rahulk29/stac-pcb/Files_for_BoardHouse/Files_for_Sierra/Final/231212_sierra_stackup_stac.pdf

# STACKUP & IMPEDANCE REPORT

Page 1 of 1

### Planner: ROOPAT Confidential / Proprietary Information Customer Required Finished Thickness: 55.00 (+5.50 / -5.50) mils

### Measured: Over mask on plated copper

### Job Name: Customer:

ch1593117-2

### Part Name:

### University of California, Berkeley STAC-V1

Revision: | Estimated Finish Thickness: 55.39 mils

### Data not provided

### Preliminary stack up:Reference only

### Stackup Notes:

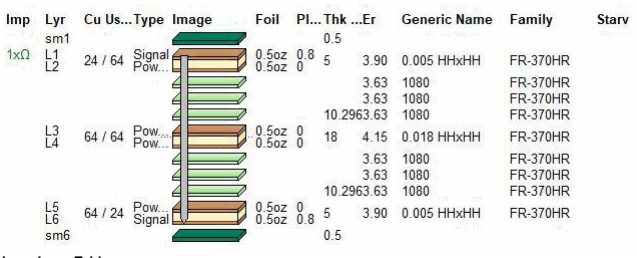
[picture p11: figure]

Index | Layer | Required Impedance [ohms] | Tol [ohms] +/- | Type | Ref 1 | Ref 2 | Orig LW [mil] | Orig Spacing [mil] | Orig CP Spacing [mil] | Finished LW [mil] | Finished Spacing [mil] | Fin. CP Spacing [mil] | Impedance Simulation [ohms] | Impedance before Mask [ohms] | IMG
a | 1 | 50 | 10% | SE Coated | | 2 | 8.10 | | | 8.50 | | | 49.7

Impedance Table

Report Version 1.60 | Report Print Date/Time: 11/21/2023 2:43:06PM | Page 1 of 1
