rahulk29/stac-pcb/schematic_review_v1/231027_bom.pdf

Purchase List: ASMPCB-STAC-V1 | Printed : 10/26/2023 2:18:02 PM

# ASMPCB-STAC-V1

ASMPCB-STAC-V1

Quantity to Build: | 1
Part List Revision: List Release Date: | A
| 10/26/2023
C:\Users\aflynn\data\PS_stuff\BWRC.mdb | Purchase List Number: | 001
Item | Qty | Part Number | Description | Reference
Vendor Name | Vendor Part Number | Manf Name | Manf Part Number
Loc | Sort Code
1 | 1 | BW-023-157 | IC custom STAC-V1 die 64 pins 0.5mm pitch QFN-64 w/EP BWRC

U6

| | DIE-CUSTOM STAC-V1
| | None

*B3

2 | 2 | BW-367-353 | Cap ceramic 0.47uF 10V 10% X7R 0603 Yageo CC0603KRX7R6BB474

C9 C12

| | CAPC-0603 0.47uF 10V
| | Digi-Key 311-1798-1-ND | Yageo CC0603KRX7R6BB474

*A2

3 | 4 | BW-171-235 | Cap ceramic 4.7uF 35V 10% X5R 0603 Murata GRM188R6YA75KE15D

C7 C8 C10 C11

| | CAPC-0603 4.7uF 35V
| | Digi-Key 490-7205-1-ND | Murata GRM188R6YA75KE15D

*A3

4 | 3 | BW-510-530 | Con 16 pin 100 mil pitch 2x8 TSW str male thru Samtec TSW-108-07-L-D

J12 J14 J15

| | CON-100 TSW 16
| | Digi-Key SAM1030-08-ND | Samtec TSW-108-07-L-D

*A8

5 | 1 | BW-350-204 | Con 6 pin 2.5mm pitch 2x3 Nano Fit RA male thru shrouded Molex 1053141106

J5

| | CON-2.5MM Nano Fit 6
| | Digi-Key WM16908-ND | Molex 1053141106

*B1

6 | 7 | BW-867-891 | Con SMA female jack end launch 50 ohm 18GHz PCB long pin (f/62mil board) Cinch 142-0701-801 J6 J8 J10 J11 J13 J16 J17
| | CON-RF SMA edge mnt
| | Digi-Key J502-ND | Cinch 142-0701-801

*B2

7 | 2 | BW-746-991 | IC LT3042 adj LDO regulator 200mA MSOP-EP-10 Analog Devices LT3042IMSE#TRPBF

U4 U5

| | IC LT3042
Digi-Key LT3042IMSE#TRPBFCT-ND | Analog Devices LT3042IMSE#TRPBF

*B4

ASMPCB-STAC-V1

Item | Qty | Part Number | Description | Reference
Vendor Name | Vendor Part Number | Manf Name | Manf Part Number
Loc | Sort Code
8 | 1 | BW-849-997 | IC LT3083 LDO regulator 3A DDPAK-5 Analog Devices LT3083EQ#PBF

U2

| | IC LT3083
Digi-Key 505-LT3083EQ#PBF-ND | Analog Devices LT3083EQ#PBF

*B5

9 | 1 | BW-747-432 | LED 565nm (green) 2.2V 0603 surface-mount Lumex SML-LX0603GW-TR

D1

| | LED green
| | Digi-Key 67-1549-1-ND | Lumex SML-LX0603GW-TR

*B7

10 | 1 | BW-471-924 | MOSFET N-CH dual 60V 35A SOT-1205 Nexperia BUK9K12-60EX

U1

| | Q-NMOS BUK9K12-60EX
| | Digi-Key 1727-1897-1-ND | Nexperia BUK9K12-60EX

*B8

11 | 3 | BW-354-763 | Res 301 1% 1/10W 0603 Panasonic ERA-3AEB3010V

R9 R12 R13

| | R1%-0603 301
| | Digi-Key P301DBCT-ND | Panasonic ERA-3AEB3010V

*C1

12 | 1 | BW-812-714 | Res 909 1% 1/10W 0603 Panasonic ERJ-3EKF9090V

R4

| | R1%-0603 909
| | Digi-Key P909HCT-ND | Panasonic ERJ-3EKF9090V

*C2

13 | 1 | BW-446-612 | Res 15K 1% 1/10W 0603 Panasonic

R8

| | R1%-0603 15K
| | Digi-Key P15.0KHCT-ND | Panasonic ERJ-3EKF1502V

*C3

14 | 1 | BW-628-791 | Res 33.2K 1% 1/10W 0603 Panasonic ERJ-3EKF3322V

R11

| | R1%-0603 33.2K
| | Digi-Key P33.2KHCT-ND | Panasonic ERJ-3EKF3322V

*C4

ASMPCB-STAC-V1

Vendor Name | Vendor Part Number | Manf Name | Manf Part Number
Loc | Sort Code
15 | 1 | BW-131-959 | Res 82.5K 1% 1/10W 0603 Panasonic ERJ-3EKF8252V

R6

| | R1%-0603 82.5K
| | Digi-Key P82.5KHCT-ND | Panasonic ERJ-3EKF8252V

*C5

16 | 1 | BW-606-753 | Res 93.1K 1% 1/10W 0603 Panasonic ERJ-3EKF9312V

R5

| | R1%-0603 93.1K
| | Digi-Key P93.1KHCT-ND | Panasonic ERJ-3EKF9312V

*C6

17 | 1 | BW-760-287 | Res 200K 1% 1/10W 0603 Panasonic ERJ-3EKF2003V

R1

| | R1%-0603 200K
| | Digi-Key P200KHCT-ND | Panasonic ERJ-3EKF2003V

*C7

18 | 1 | BW-560-201 | Res 215K 1% 1/10W 0603 Panasonic ERJ-3EKF2153V

R7

| | R1%-0603 215K
| | Digi-Key P215KHCT-ND | Panasonic ERJ-3EKF2153V

*C8

19 | 1 | BW-514-032 | Res 510K 1% 1/10W 0603 Panasonic ERJ-3EKF5103V

R2

| | R1%-0603 510K
| | Digi-Key P510KHCT-ND | Panasonic ERJ-3EKF5103V

*D1

20 | 1 | BW-421-162 | Res 2.7M 5% 1/10W 0603 Panasonic ERJ-3GEYJ275V

R3

| | R5%-0603 2.7M
| | Digi-Key P2.7MGCT-ND | Panasonic ERJ-3GEYJ275V

*D2

21 | 1 | BW-257-784 | Res var trimmer pot 5K 1/4W 3-pin SMT Bourns 3214X-1-502E

R10

| | RVAR 5K
Digi-Key 3214X-1-502ECT-ND | Bourns 3214X-1-502E

*D3

ASMPCB-STAC-V1

Vendor Name | Vendor Part Number | Manf Name | Manf Part Number
Loc | Sort Code
22 | 1 | BW-431-238 | Switch slide SPDT ST thru Wurth 450301014042

S1

| | SW SPDT
Digi-Key 450301014042-ND | Wurth 450301014042

*D4

23 | 1 | BW-966-768 | Test point loop 63mil dia hole black Keystone 5006

T9

| | TEST-PT 1
| | Digi-Key 36-5006-ND | Keystone 5006

*D6

24 | 2 | BW-220-198 | Con 12 pin 100 mil pitch 2x5 TSW RA male thru 0.230" post height Samtec TSW-106-08-L-D-RA J7 J9
| | CON-100 TSW 12
| | Digikey SAM1041-06-ND | Samtec TSW-106-08-L-D-RA

*A7

25 | 1 | BW-663-053 | Cap ceramic 0.1uF 16V 5% X7R 0603 Kemet C0603C104J4RACTU

C6

| | CAPC-0603 0.1uF 16V
| | Mouser 80-C0603C104J4R | Kemet C0603C104J4RACTU

*A1

Digi-Key 399-1097-1-ND

26 | 10 | BW-224-068 | Cap ceramic 10uF 25V 20% X5R 0603 Murata GRM188R61E106MA73D

C4 C5 C15 C16 C17 C18 C19
C20 C21 C22
| | CAPC-0603 10uF 25V
Mouser 81-GRM188R61E106MA3D | Murata GRM188R61E106MA73D

*A4

Digi-Key 490-7202-1-ND

27 | 5 | BW-998-821 | Cap aluminum polymer 220uF 16V 20% SMD, 6.3mm dia. Panasonic 16SVPK220M

C1 C2 C3 C13 C14

| | CAPE-AL-GP 220uF 16V
| | Mouser 667-16SVPK220M | Panasonic 16SVPK220M

*A5

28 | 4 | BW-517-054 | Con 3 pin 100 mil pitch 1x3 TSW str male thru 0.230" post height Samtec TSW-103-07-G-S

J1 J2 J3 J4

| | CON-100 TSW 3
| | Mouser 200-TSW10307GS | Samtec TSW-103-07-G-S

*A6

Digi-Key SAM1029-03-ND

ASMPCB-STAC-V1

Vendor Name | Vendor Part Number | Manf Name | Manf Part Number
Loc | Sort Code
29 | 1 | BW-843-693 | IC LTC4365CTS8#TRMPBF
Analog Devices LTC4365 Surge Surpressor

U3

IC LTC4365CTS8#TRMPBF

Mouser | 584-C4365CTS8TRMPBF | Analog Devices | LTC4365CTS8#TRMPBF

*B6

30 | 1 | BW-602-053 | Test point loop 63mil dia hole orange
Keystone 5008

T4

TEST-PT 1

Mouser | 534-5008 | Keystone | 5008

*D5

Digi-Key 36-5008-ND

ASMPCB-STAC-V1
