rahulk29/stac-pcb/Files_for_AssemblyHouse/Digicom_Final/240109_stac_v1_fabrication_drawing.PDF

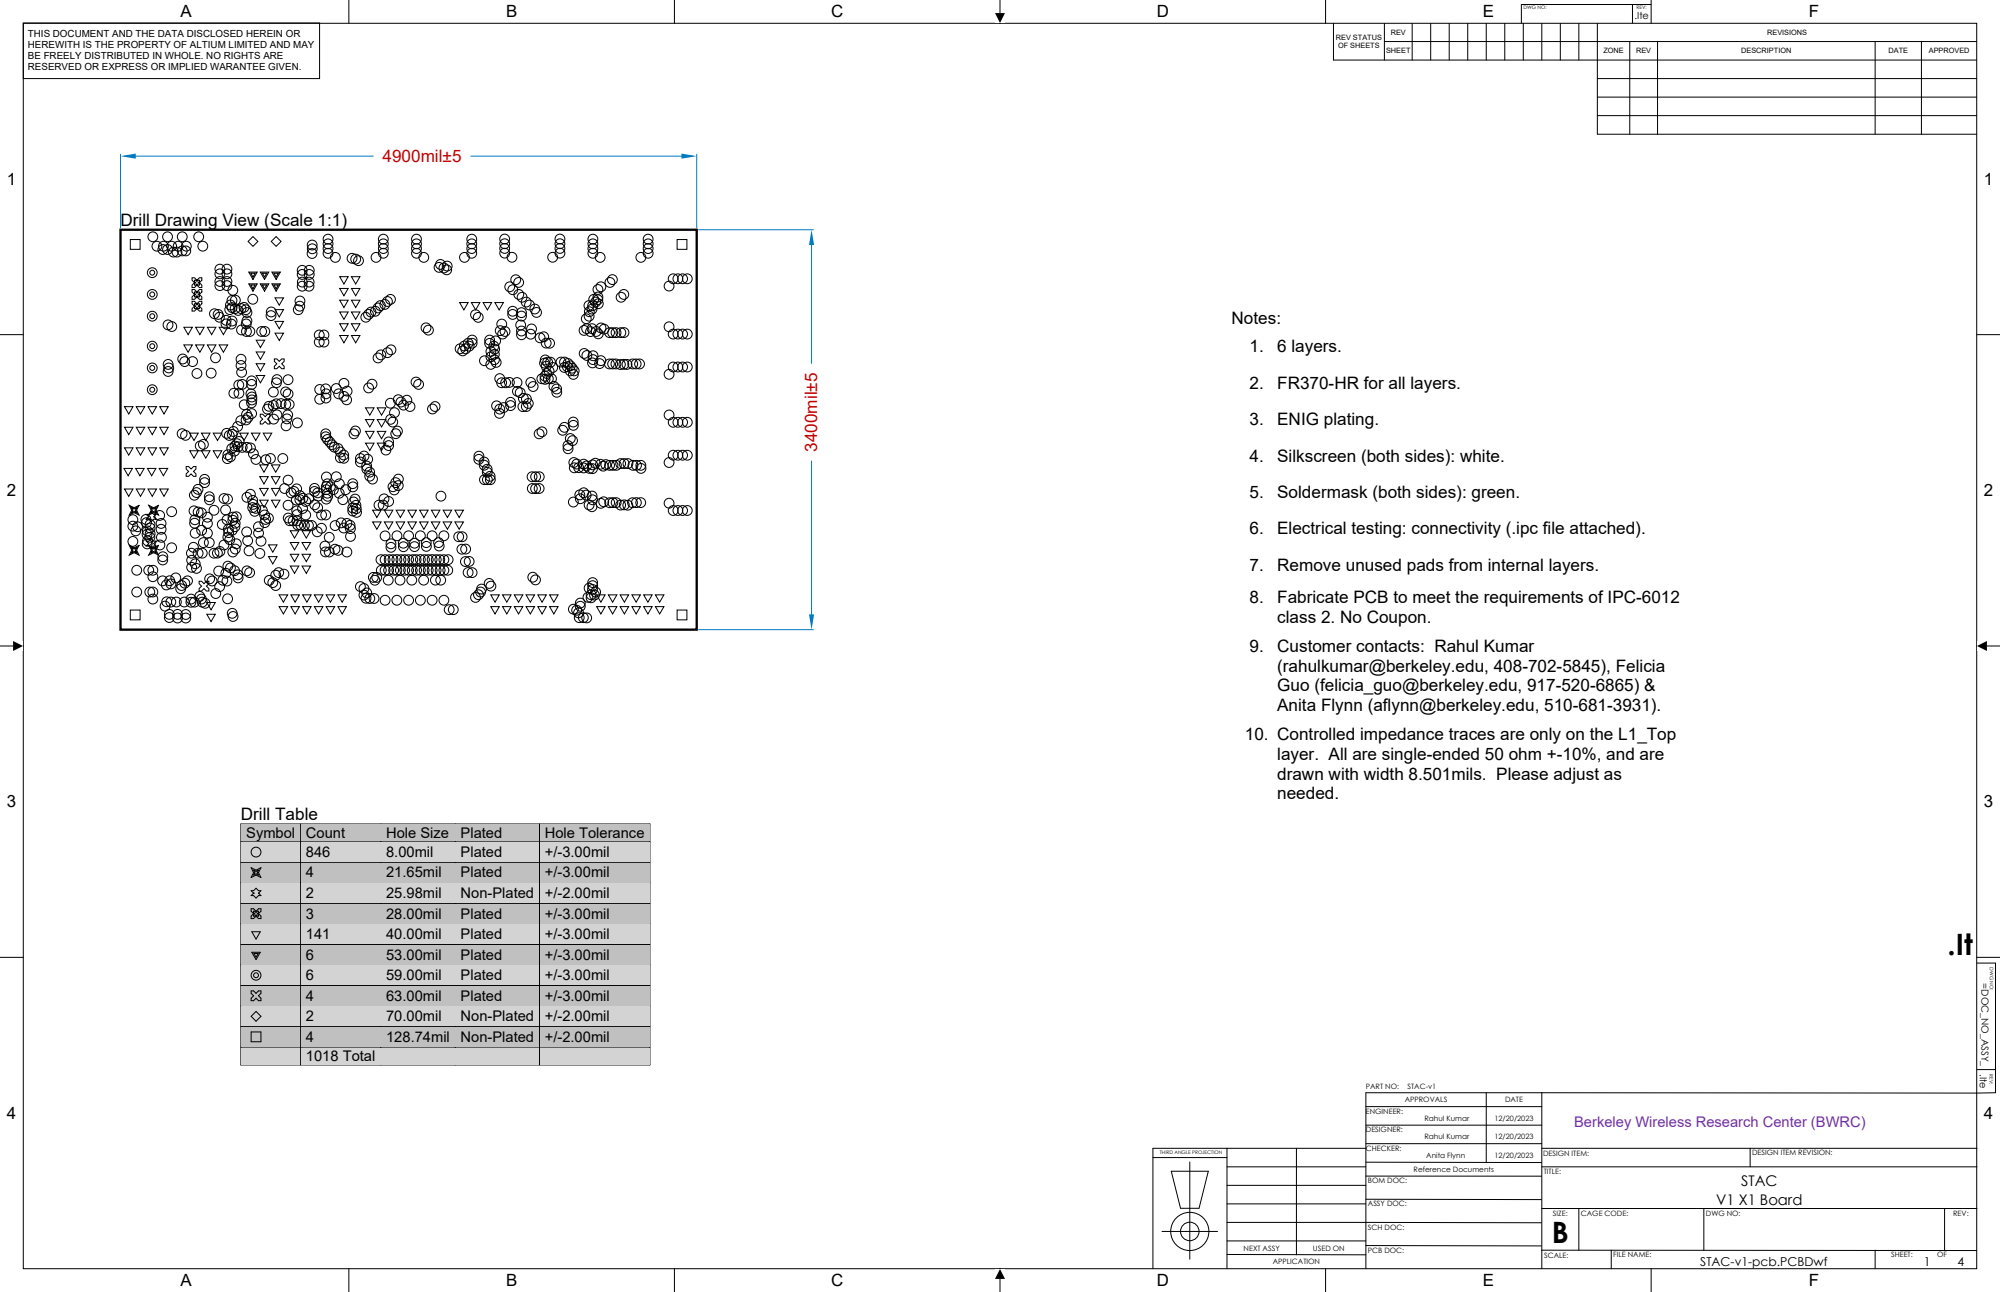
[picture p59: page 1]

HEREWITH IS THE PROPERTY OF ALTIUM LIMITED AND MAY
BE FREELY DISTRIBUTED IN WHOLE. NO RIGHTS ARE
RESERVED OR EXPRESS OR IMPLIED WARANTEE GIVEN.

Drill Drawing View (Scale 1:1)

2. FR370-HR for all layers.

4. Silkscreen (both sides): white.

5. Soldermask (both sides): green.

6. Electrical testing: connectivity (.ipc file attached).

7. Remove unused pads from internal layers.
Fabricate PCB to meet the requirements of IPC-6012
class 2. No Coupon.
Customer contacts: Rahul Kumar
(rahulkumar@berkeley.edu, 408-702-5845), Felicia
Guo (felicia_guo@berkeley.edu, 917-520-6865) &
Anita Flynn (aflynn@berkeley.edu, 510-681-3931).
Controlled impedance traces are only on the L1_Top
layer. All are single-ended 50 ohm +-10%, and are
drawn with width 8.501mils. Please adjust as
needed.

Symbol | Count | Hole Size | Plated | Hole Tolerance

846 | 8.00mil | Plated | +/-3.00mil
4 | 21.65mil | Plated | +/-3.00mil
2 | 25.98mil | Non-Plated | +/-2.00mil
3 | 28.00mil | Plated | +/-3.00mil
141 | 40.00mil | Plated | +/-3.00mil
6 | 53.00mil | Plated | +/-3.00mil
6 | 59.00mil | Plated | +/-3.00mil
4 | 63.00mil | Plated | +/-3.00mil
2 | 70.00mil | Non-Plated | +/-2.00mil
4 | 128.74mil | Non-Plated | +/-2.00mil
1018 Total

APPROVALS | DATE

ENGINEER: Rahul Kumar | 12/20/2023

Berkeley Wireless Research Center (BWRC)

DESIGNER: Rahul Kumar | 12/20/2023

THIRD ANGLE PROJECTION

CHECKER: Anita Flynn | 12/20/2023

SCH DOC:

NEXT ASSY | USED ON

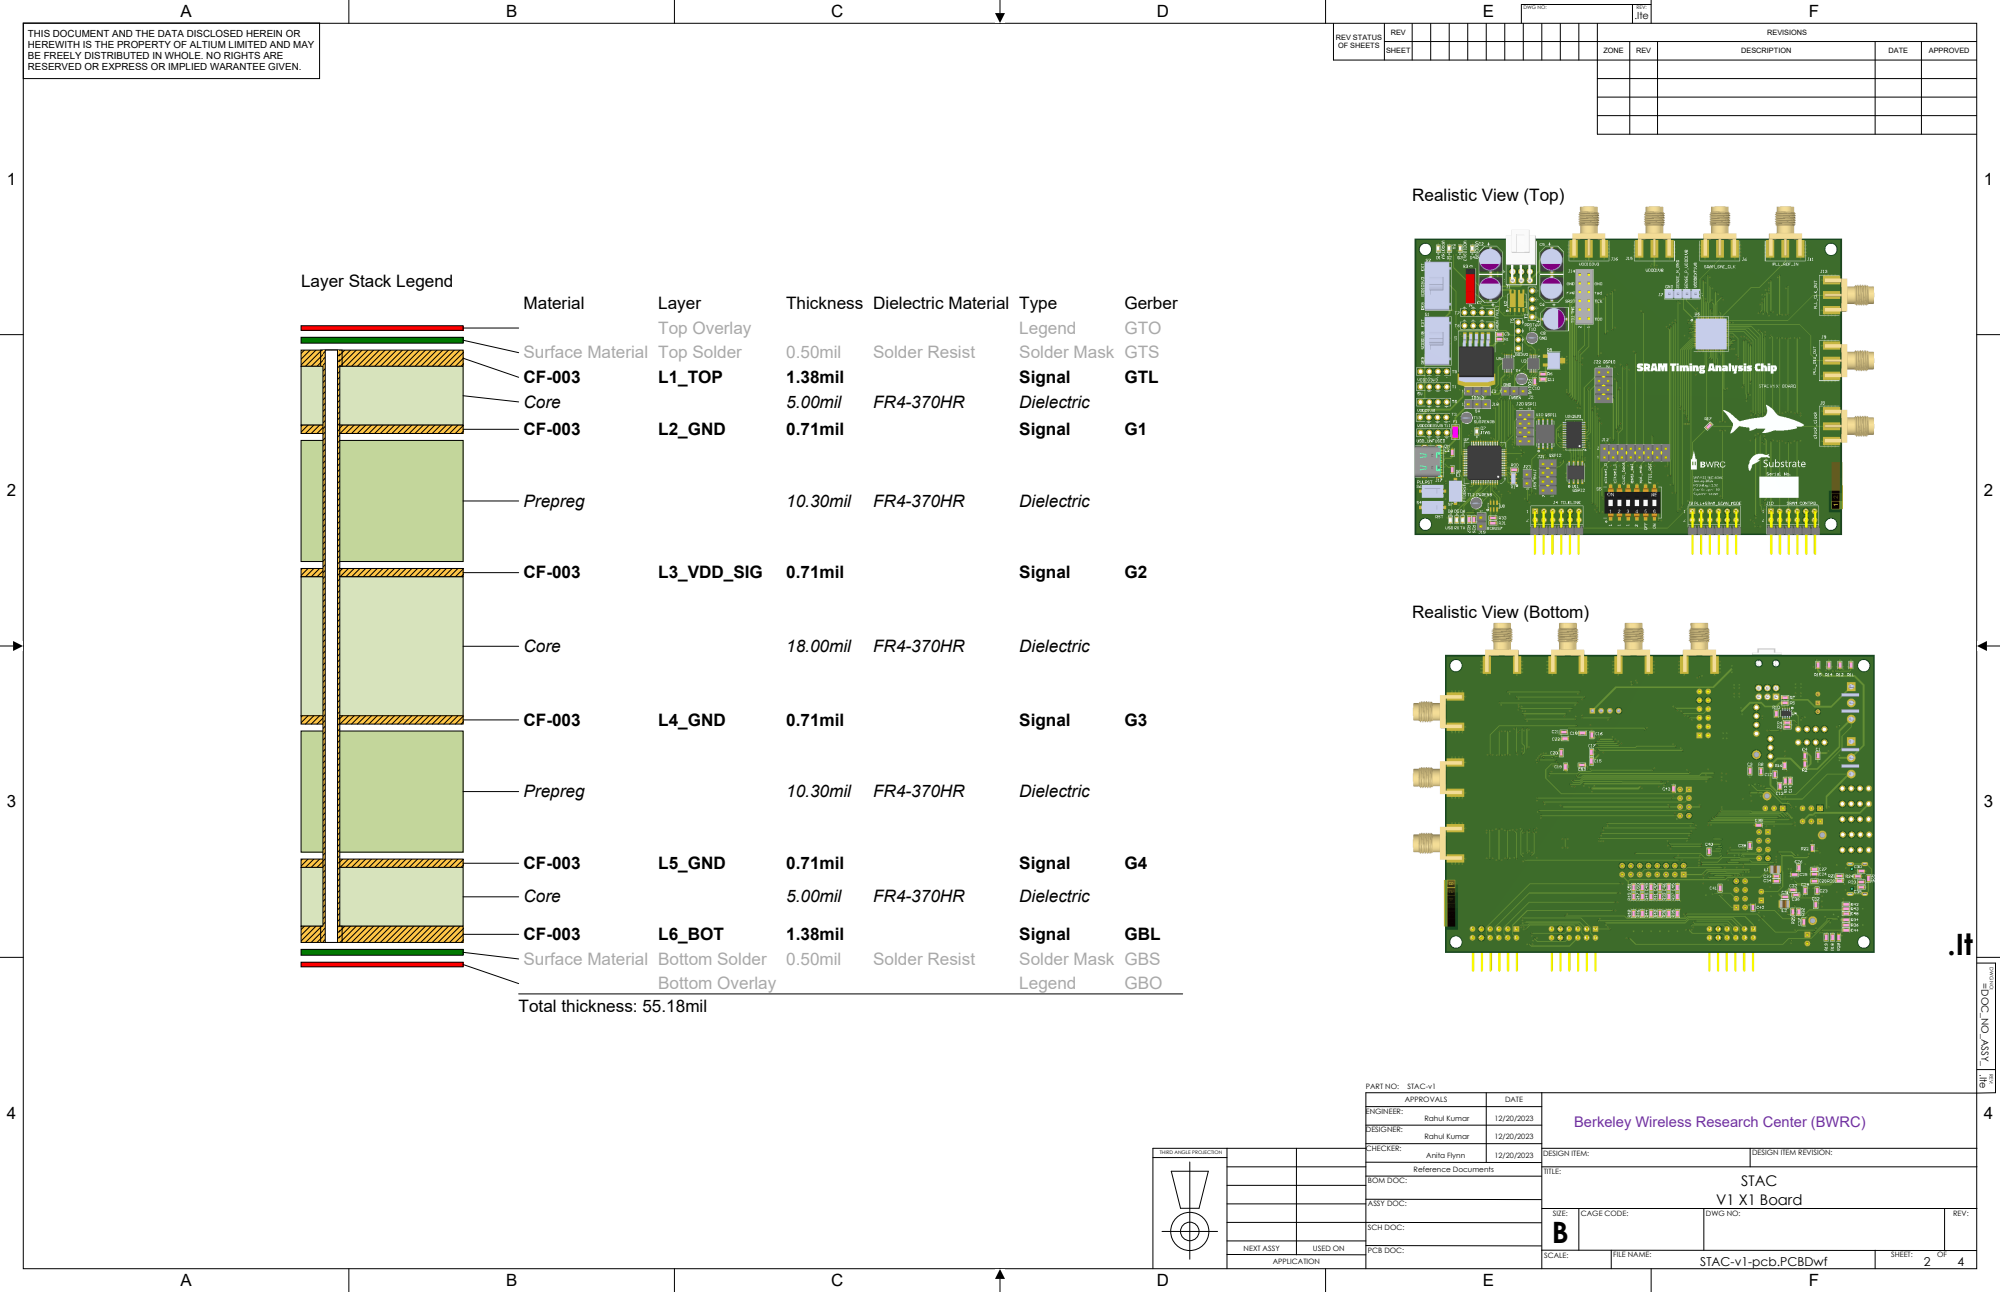
[picture p60: page 2]

APPROVALS | DATE

ENGINEER: Rahul Kumar | 12/20/2023

Berkeley Wireless Research Center (BWRC)

DESIGNER: Rahul Kumar | 12/20/2023

THIRD ANGLE PROJECTION

CHECKER: Anita Flynn | 12/20/2023

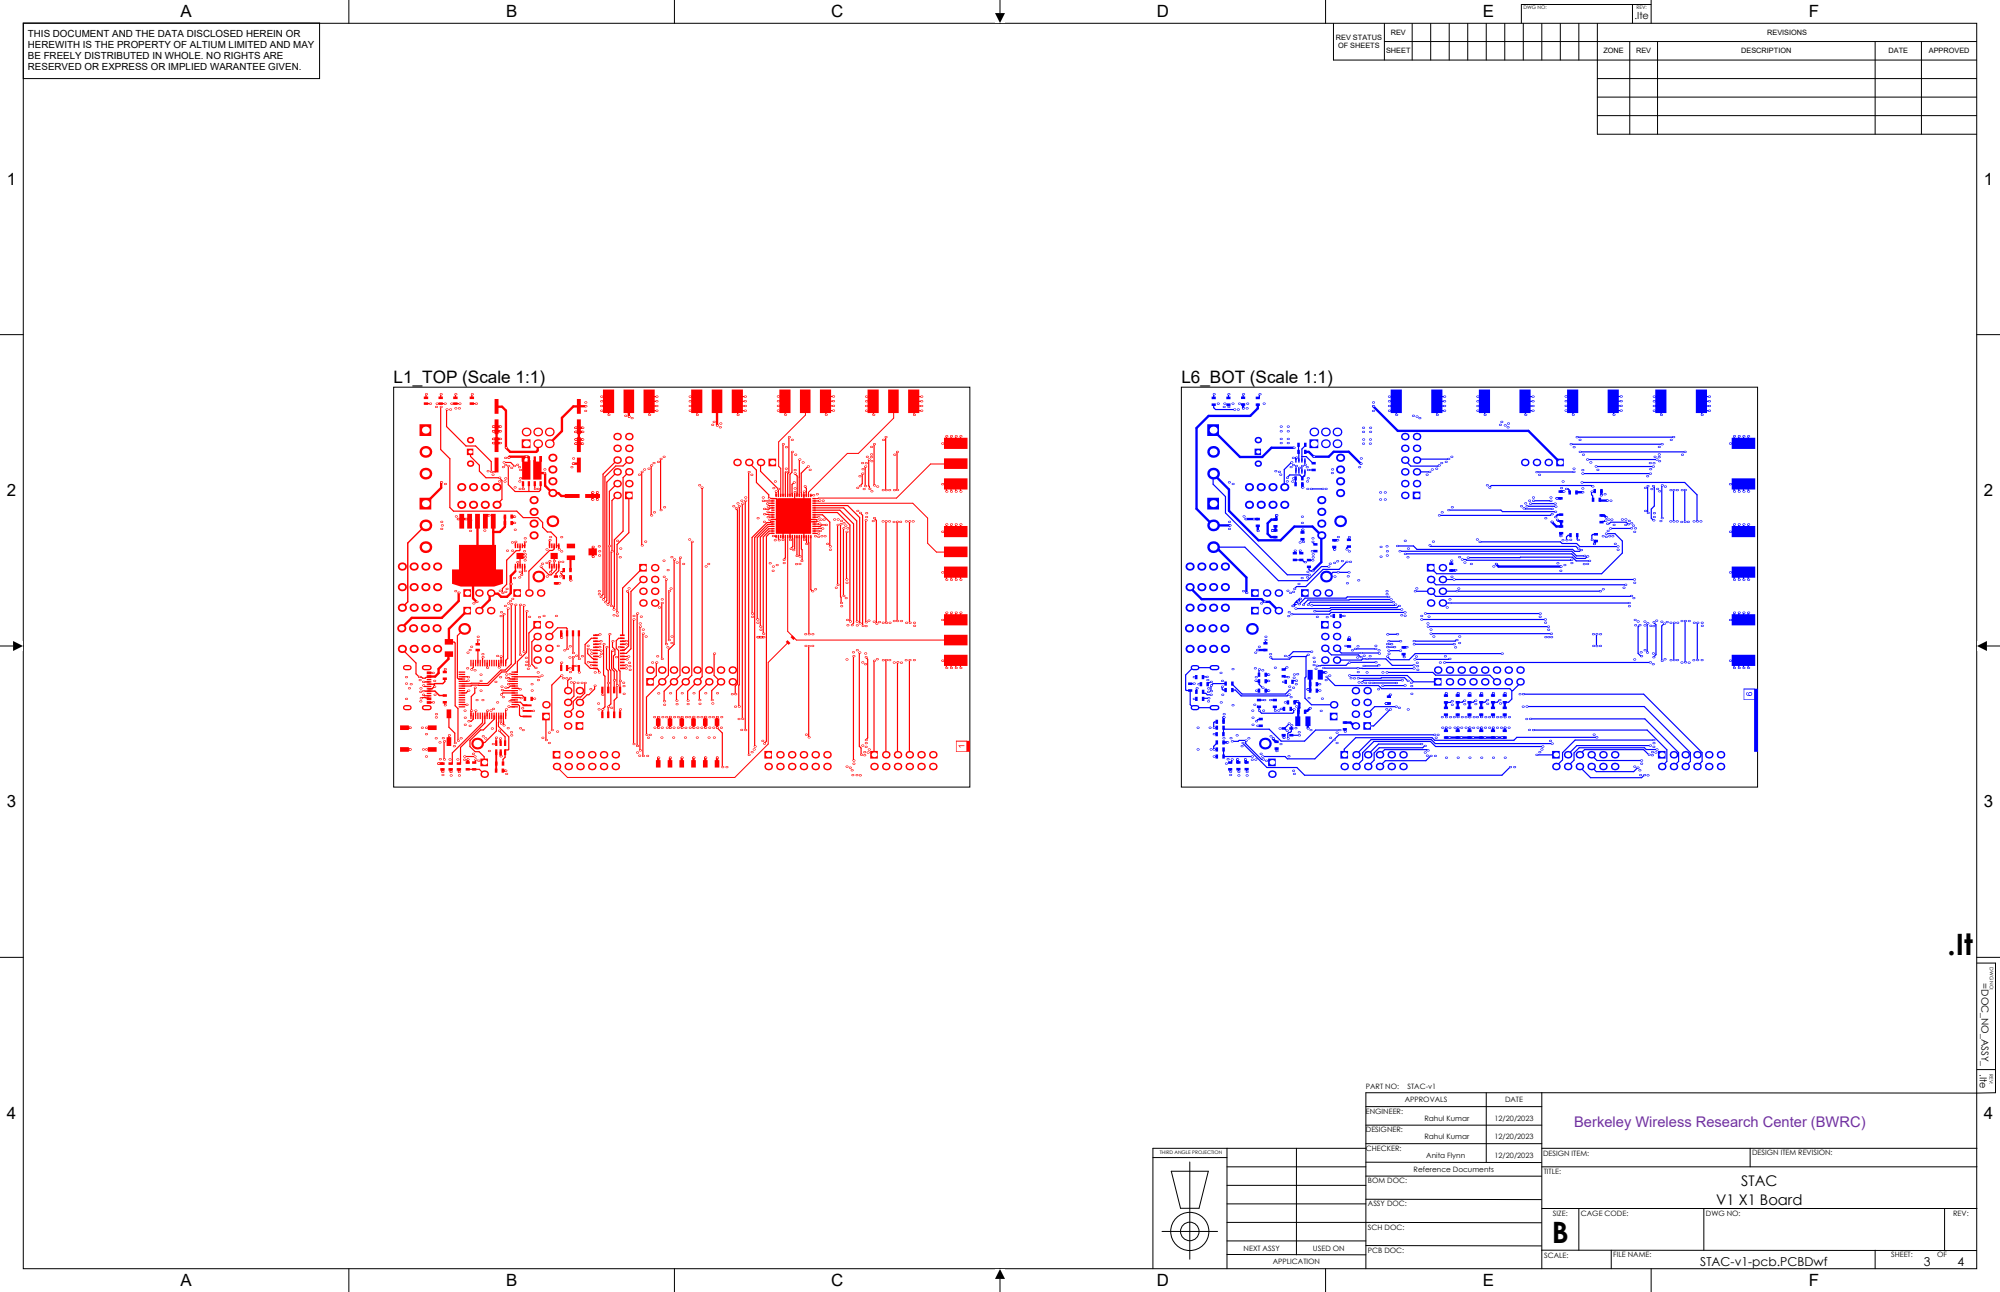
[picture p61: page 3]

Berkeley Wireless Research Center (BWRC)

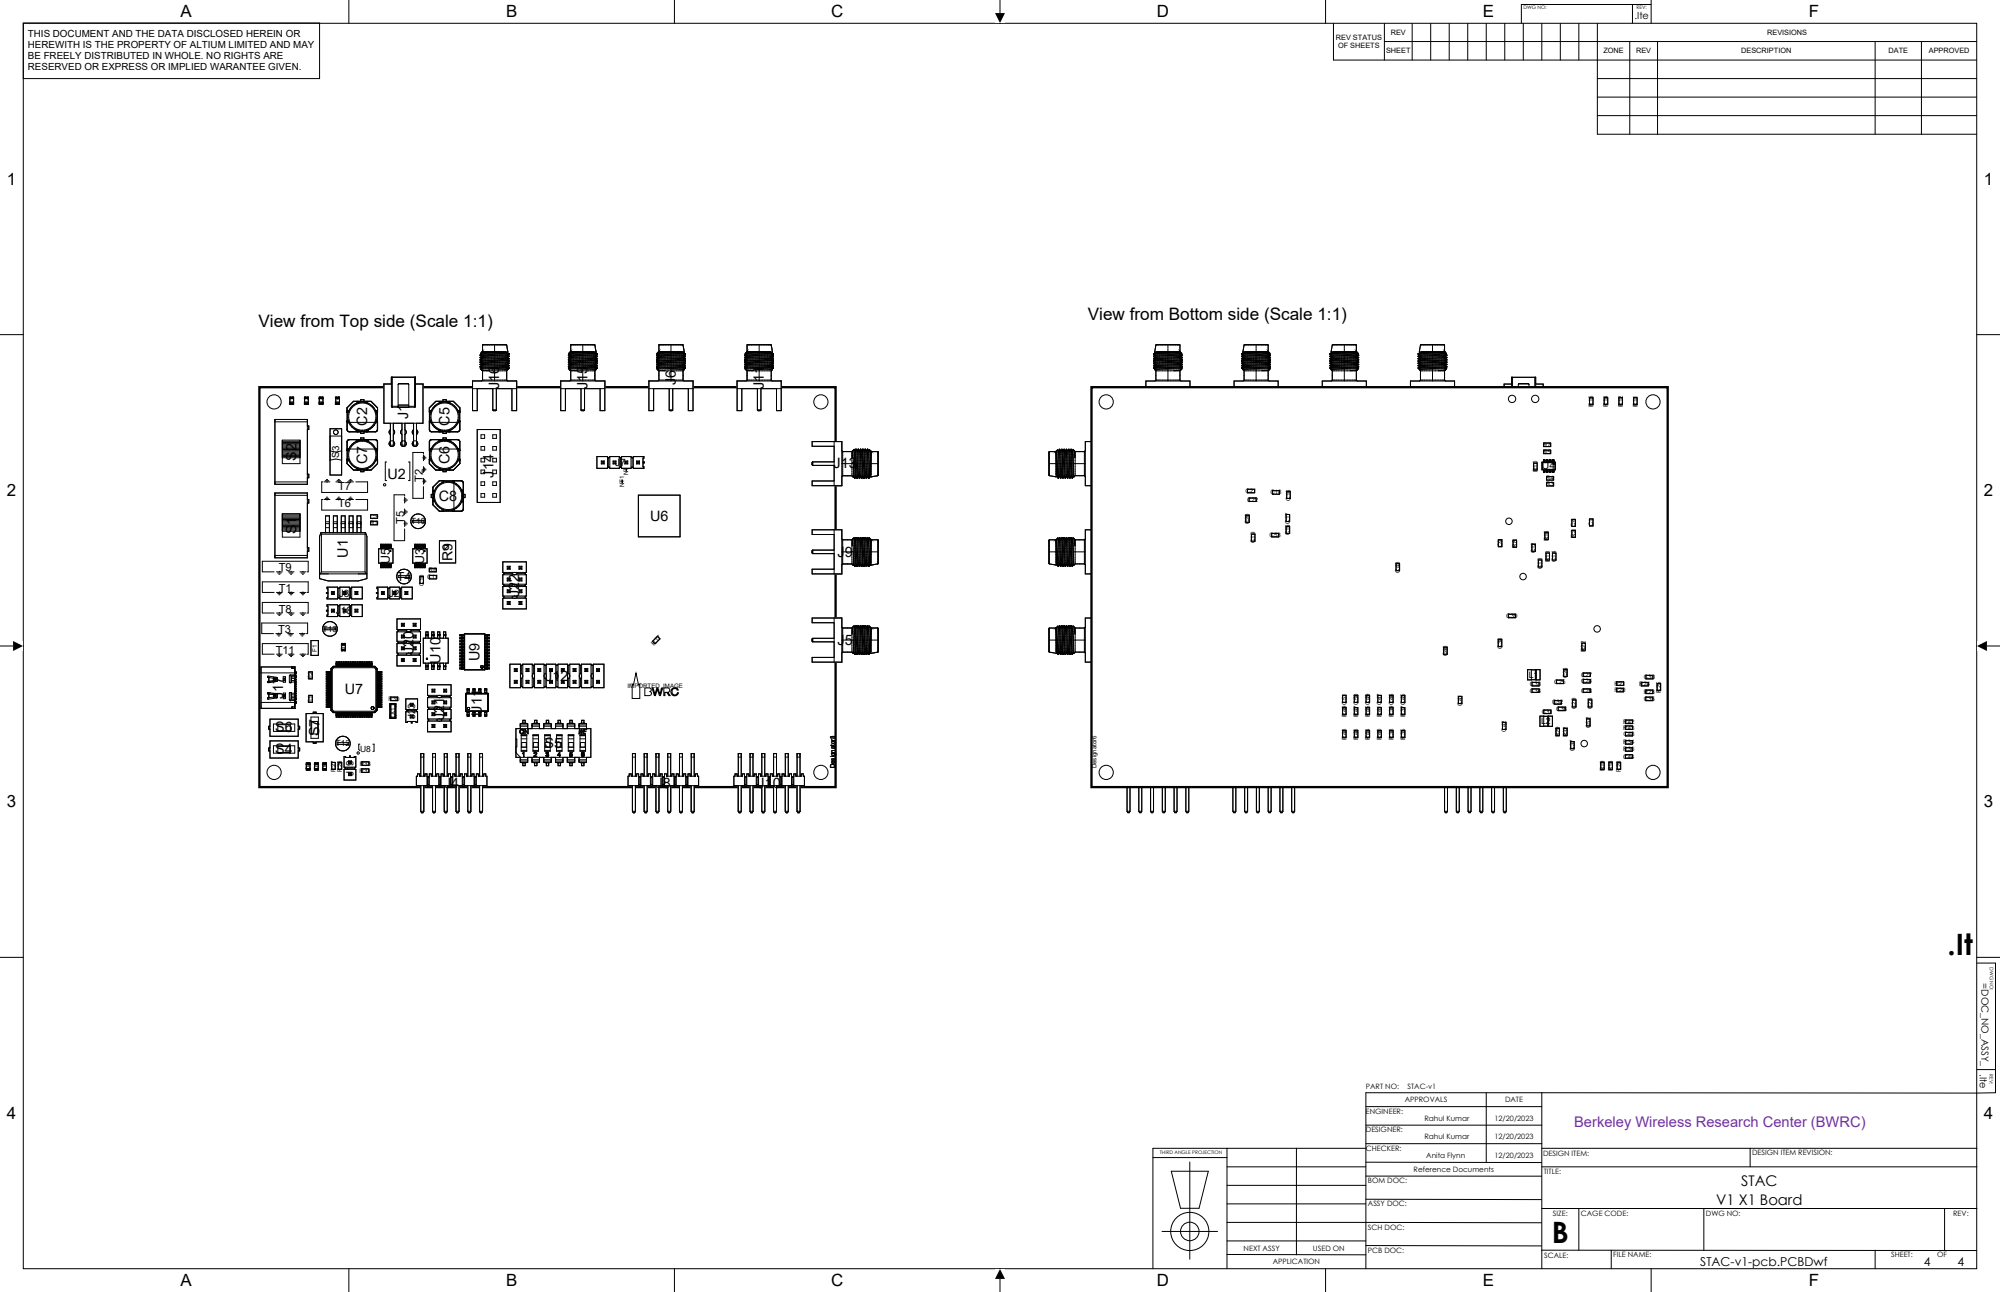
[picture p62: page 4]

View from Bottom side (Scale 1:1)

View from Top side (Scale 1:1)

Berkeley Wireless Research Center (BWRC)
