rahulk29/stac-pcb/Files_for_AssemblyHouse/Digicom_Final/240109_stac_v1_SMT.pdf

# stac-v1.bmb 1/9/2024 File By: bob@partsync.com www.PartSync.com Flags: X=no-stuff T=Thru Hole H=Hand SMT E=Error

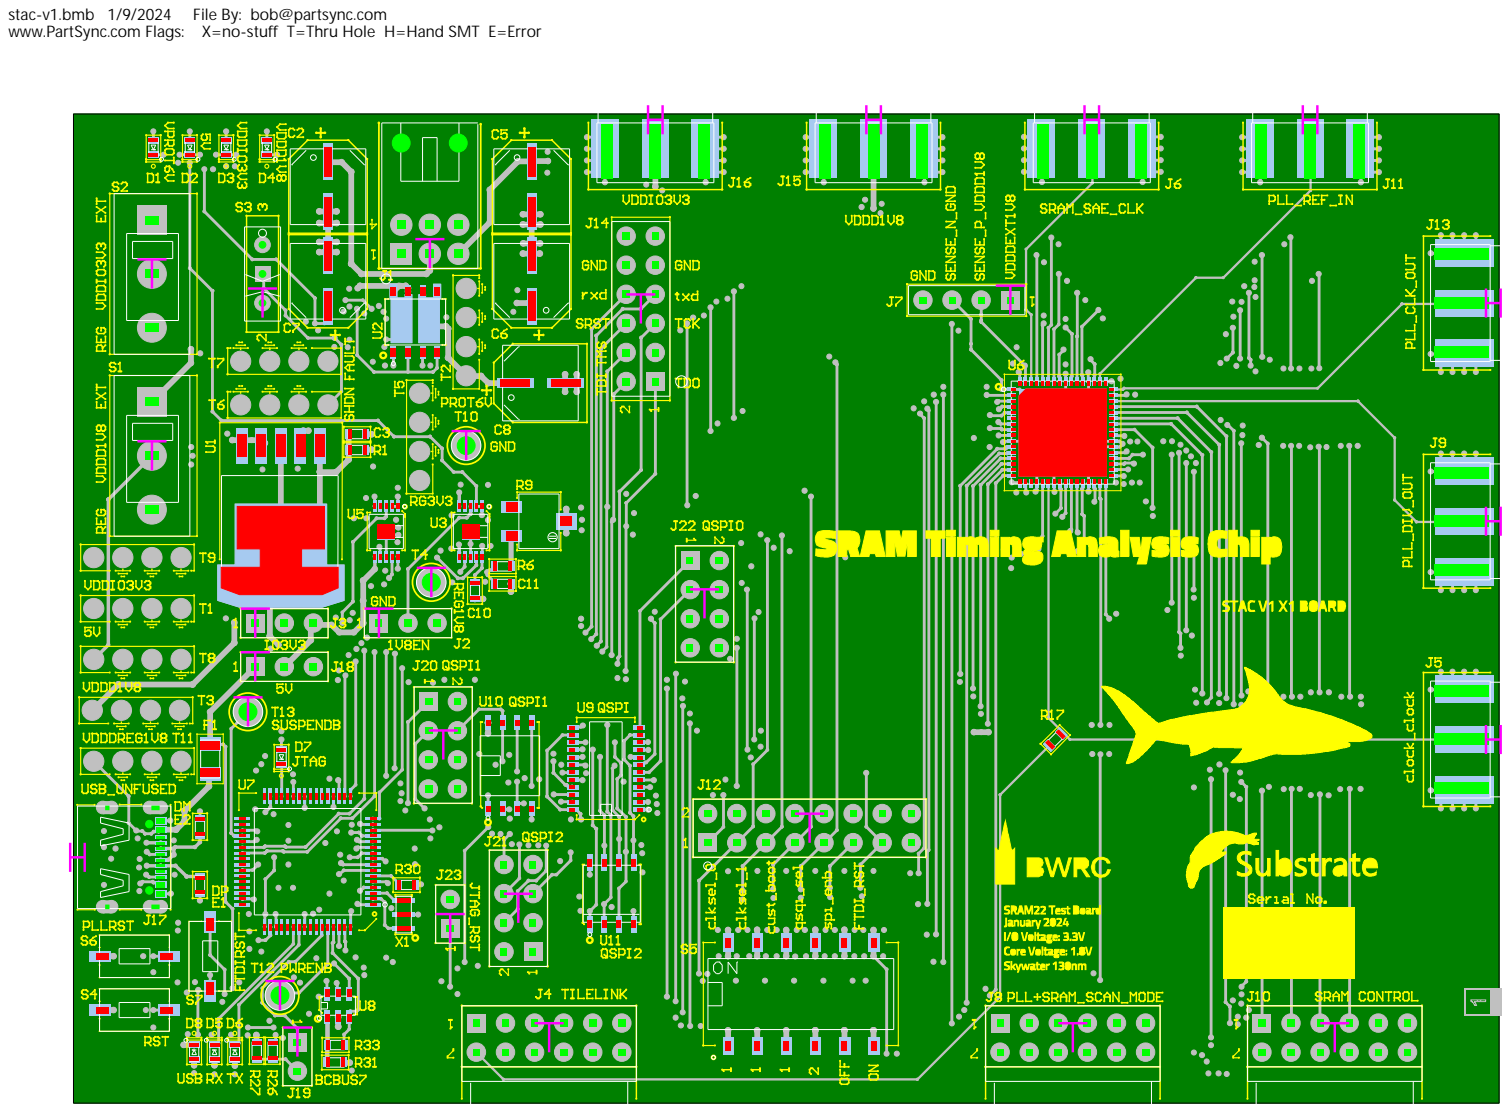
[picture p63: page 1]

# stac-v1.bmb 1/9/2024 File By: bob@partsync.com www.PartSync.com Flags: X=no-stuff T=Thru Hole H=Hand SMT E=Error

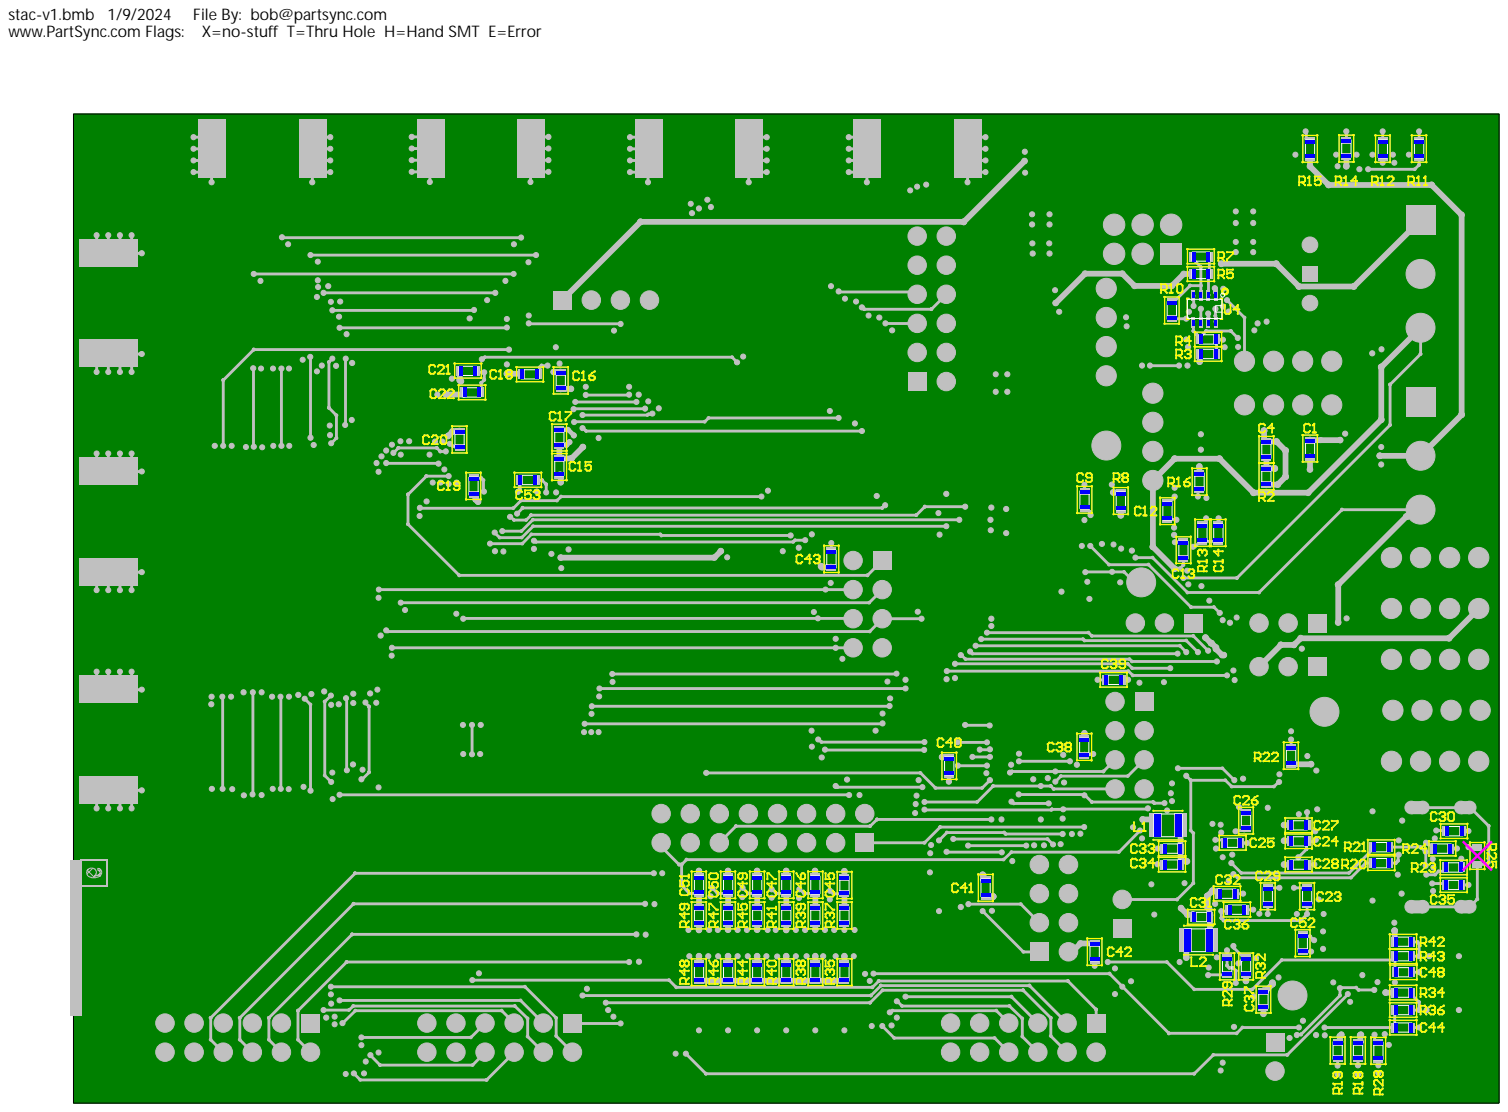
[picture p64: page 2]
