rahulk29/stac-pcb/Files_for_AssemblyHouse/Digicom_RFQ/fab_drawing_stac.pdf

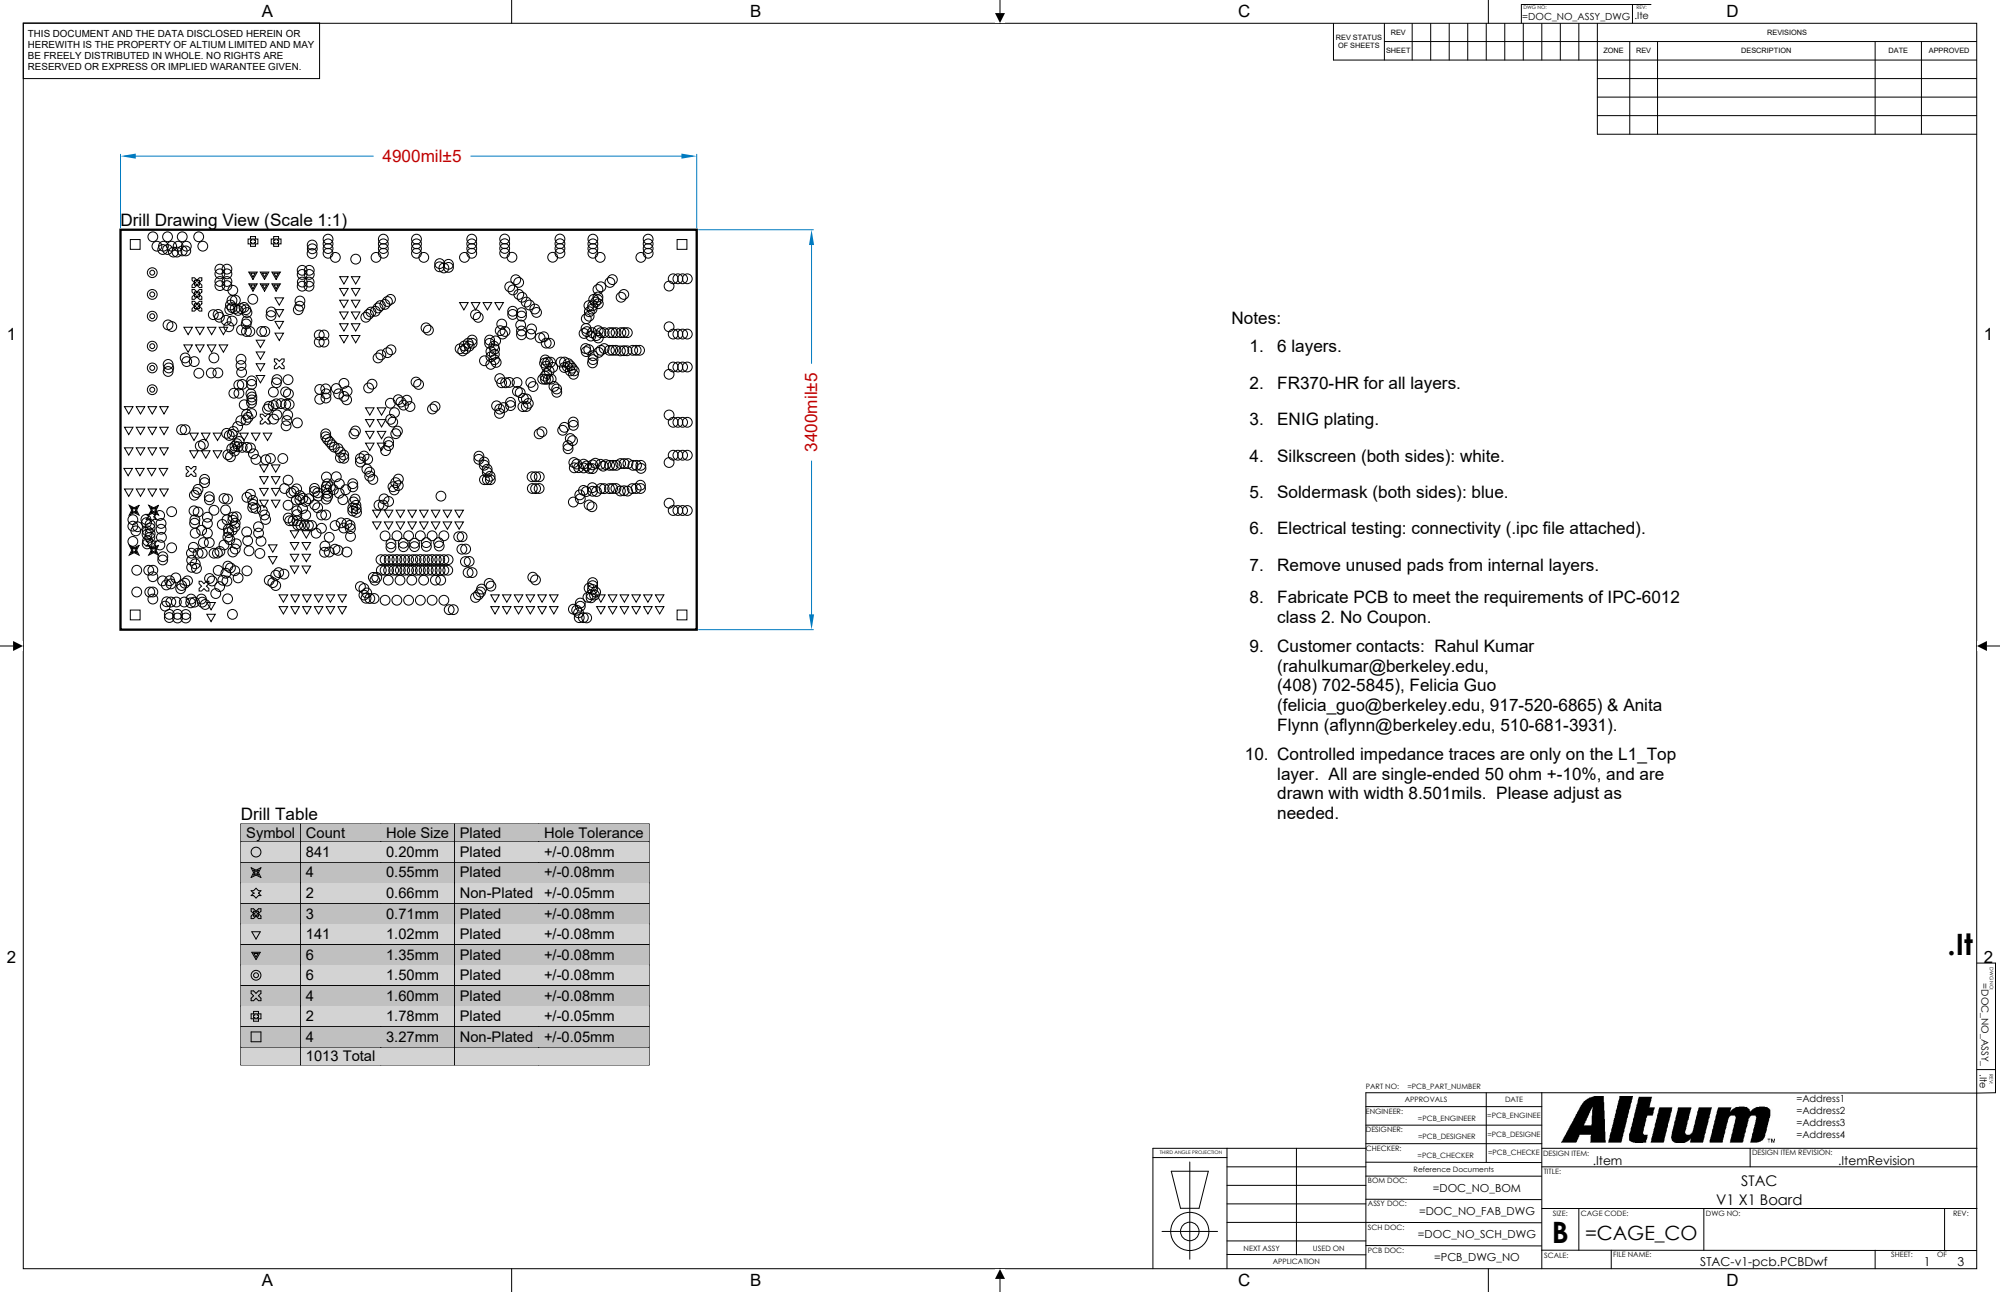
[picture p65: page 1]

HEREWITH IS THE PROPERTY OF ALTIUM LIMITED AND MAY
BE FREELY DISTRIBUTED IN WHOLE. NO RIGHTS ARE
RESERVED OR EXPRESS OR IMPLIED WARANTEE GIVEN.

Drill Drawing View (Scale 1:1)

2. FR370-HR for all layers.

4. Silkscreen (both sides): white.

5. Soldermask (both sides): blue.

6. Electrical testing: connectivity (.ipc file attached).

7. Remove unused pads from internal layers.
Fabricate PCB to meet the requirements of IPC-6012
class 2. No Coupon.
Customer contacts: Rahul Kumar
(rahulkumar@berkeley.edu,
(408) 702-5845), Felicia Guo
(felicia_guo@berkeley.edu, 917-520-6865) & Anita
Flynn (aflynn@berkeley.edu, 510-681-3931).
Controlled impedance traces are only on the L1_Top
layer. All are single-ended 50 ohm +-10%, and are
drawn with width 8.501mils. Please adjust as
needed.

Symbol | Count | Hole Size | Plated | Hole Tolerance

841 | 0.20mm | Plated | +/-0.08mm
4 | 0.55mm | Plated | +/-0.08mm
2 | 0.66mm | Non-Plated | +/-0.05mm
3 | 0.71mm | Plated | +/-0.08mm
141 | 1.02mm | Plated | +/-0.08mm
6 | 1.35mm | Plated | +/-0.08mm
6 | 1.50mm | Plated | +/-0.08mm
4 | 1.60mm | Plated | +/-0.08mm
2 | 1.78mm | Plated | +/-0.05mm
4 | 3.27mm | Non-Plated | +/-0.05mm
1013 Total

APPROVALS | DATE

ENGINEER: =PCB_ENGINEER | =PCB_ENGINEE

DESIGNER: =PCB_DESIGNER | =PCB_DESIGNE

THIRD ANGLE PROJECTION

CHECKER: =PCB_CHECKER | =PCB_CHECKE

SCH DOC: =DOC_NO_SCH_DWG

NEXT ASSY | USED ON

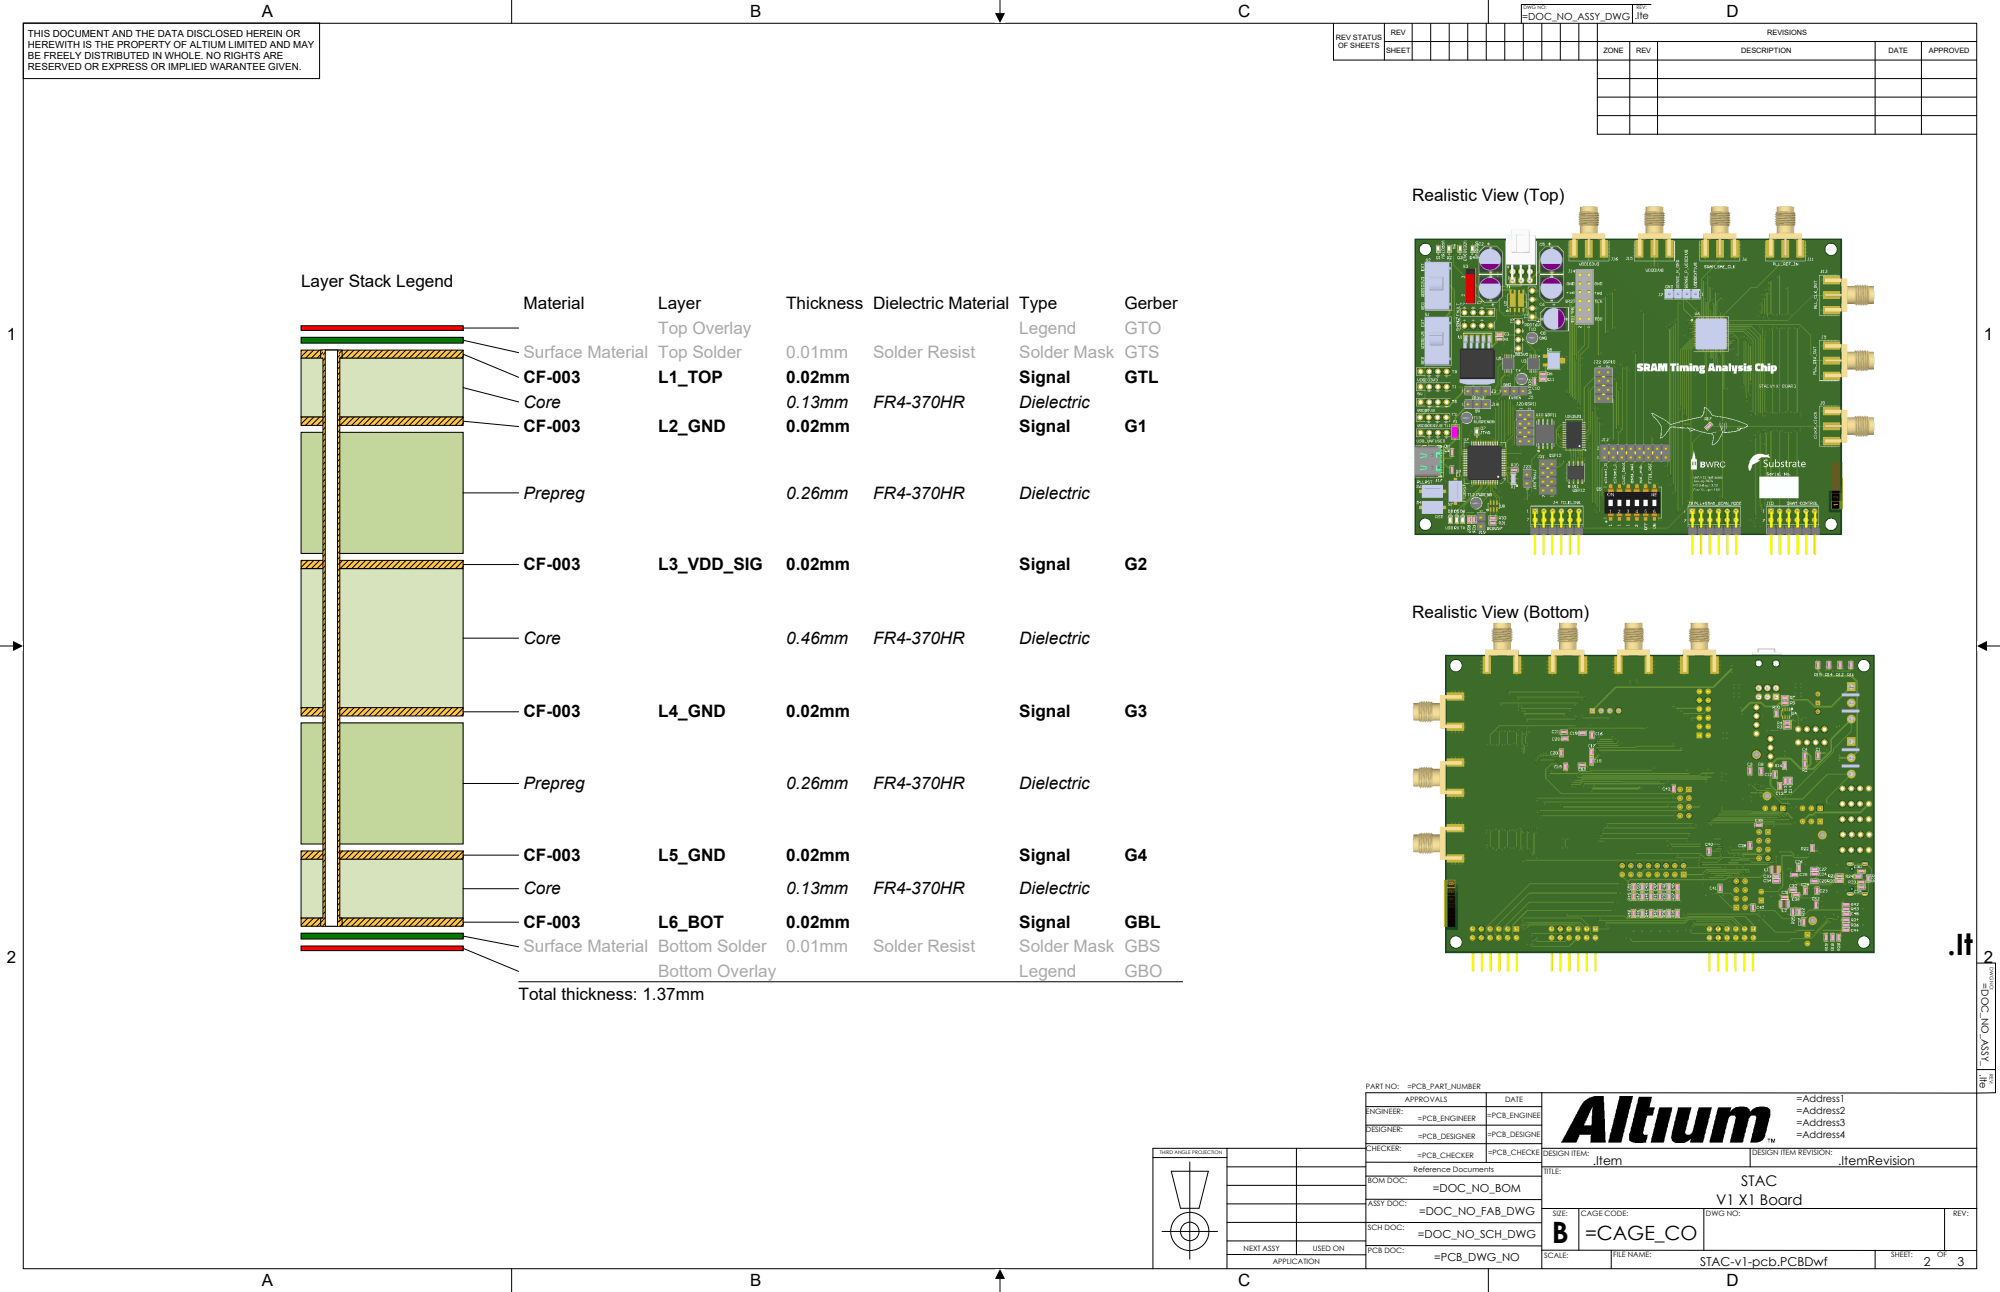
[picture p66: page 2]

APPROVALS | DATE

ENGINEER: =PCB_ENGINEER | =PCB_ENGINEE

DESIGNER: =PCB_DESIGNER | =PCB_DESIGNE

THIRD ANGLE PROJECTION

CHECKER: =PCB_CHECKER | =PCB_CHECKE

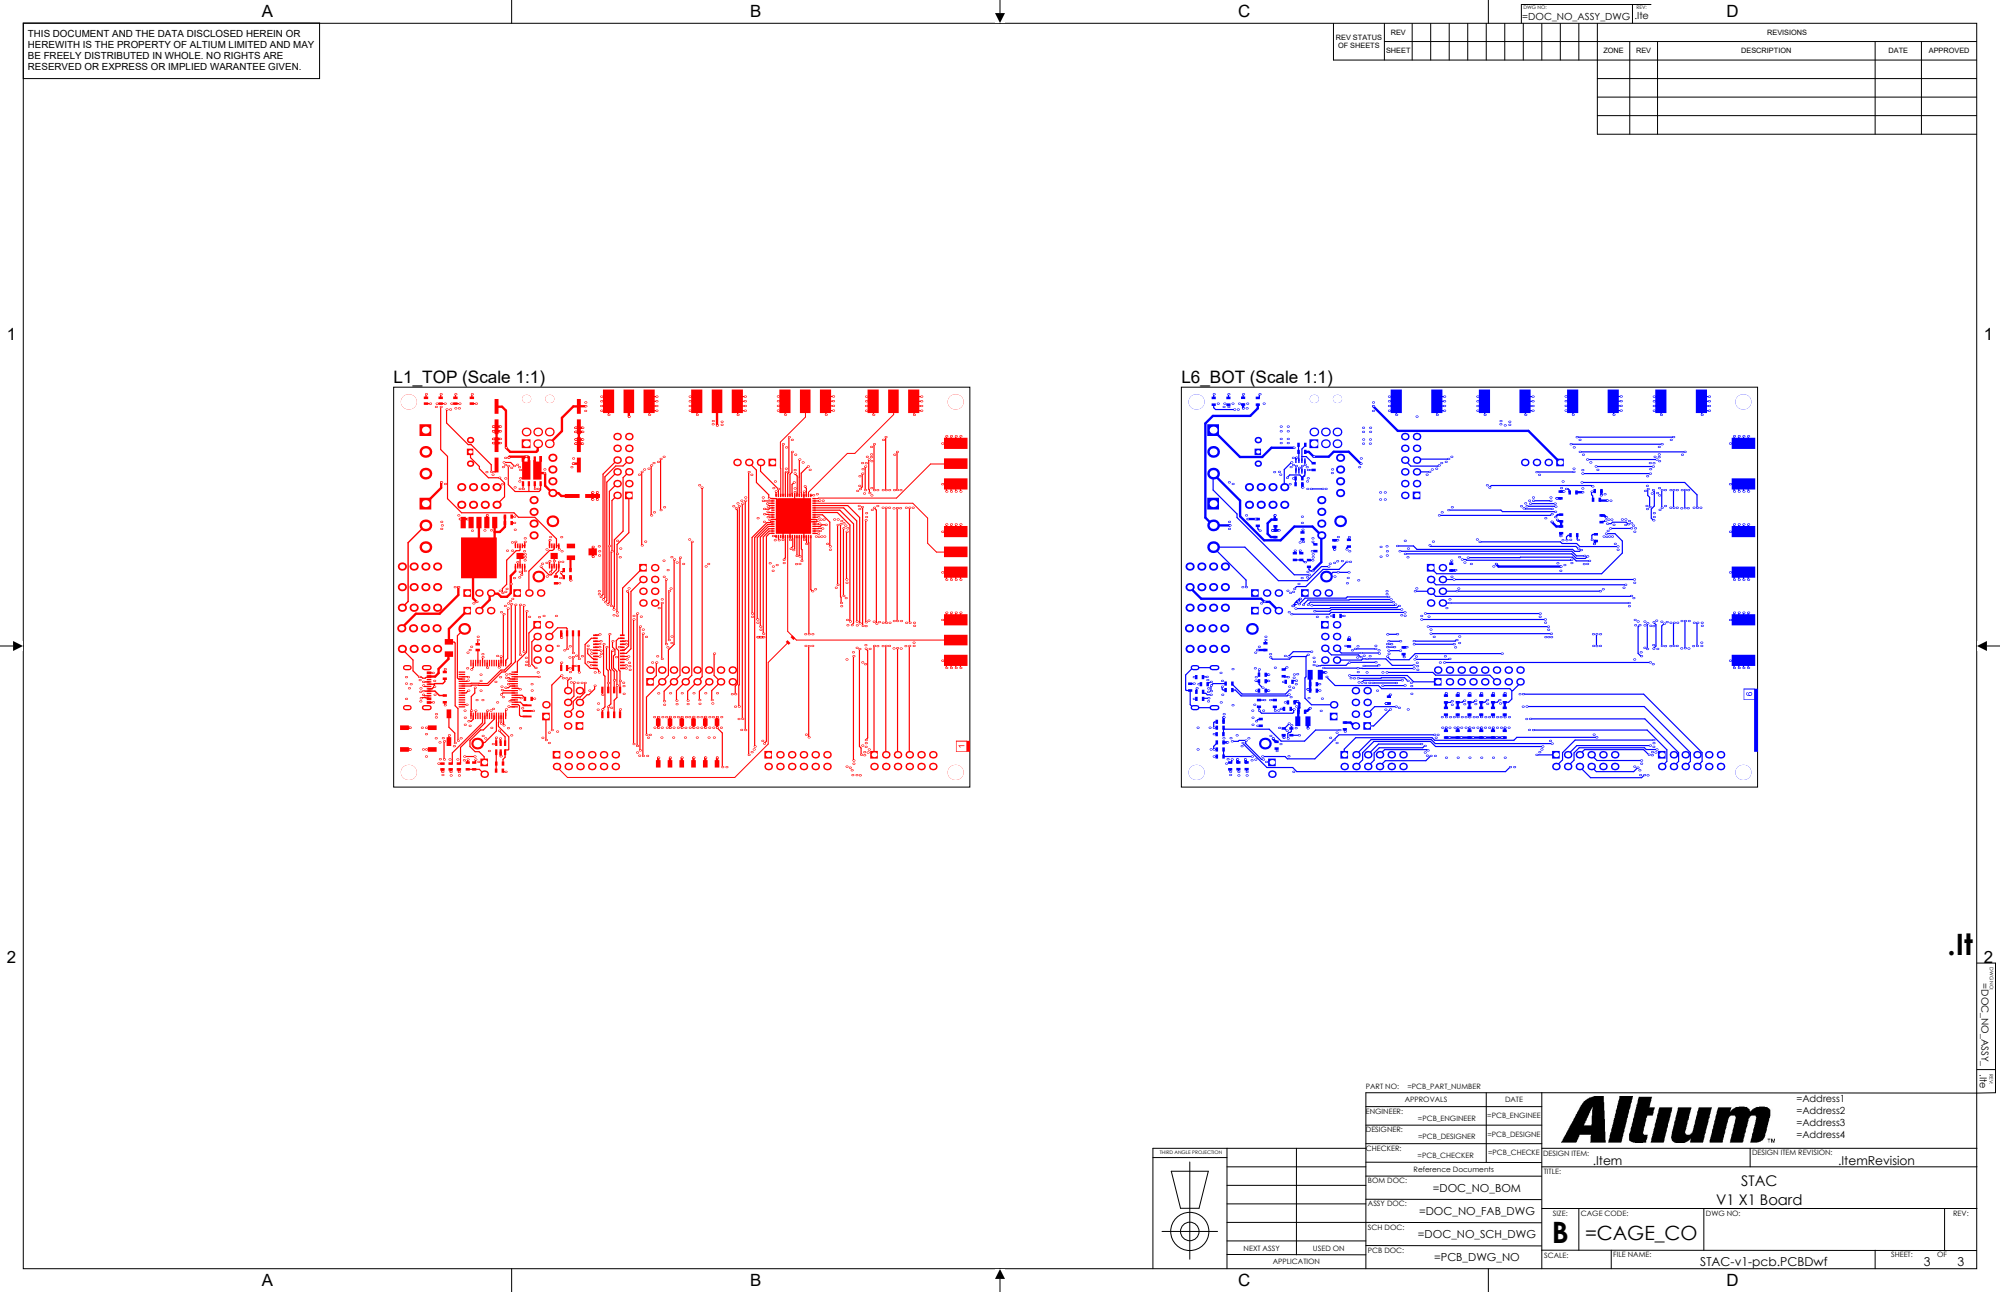
[picture p67: page 3]
