rahulk29/stac-pcb/Files_for_AssemblyHouse/Digicom_RFQ/stac-v1_SMT.pdf

# stac-v1.bmb 12/13/2023 File By: bob@partsync.com www.PartSync.com Flags: X=no-stuff T=Thru Hole H=Hand SMT E=Error

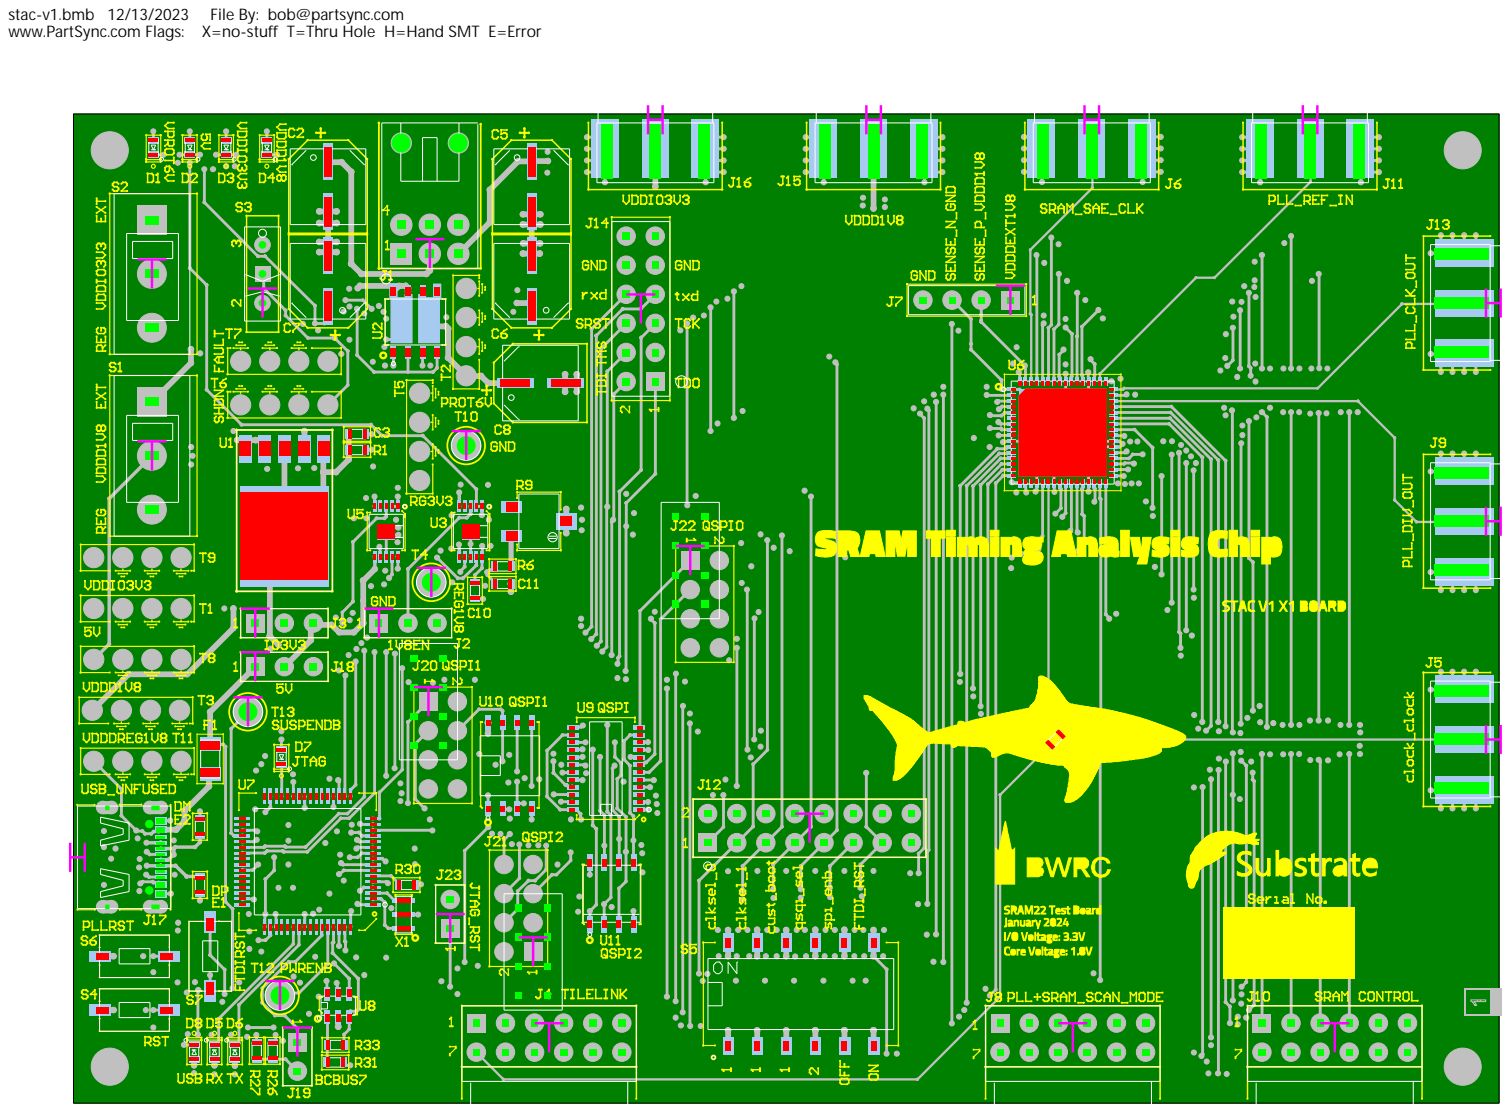
[picture p68: page 1]

# stac-v1.bmb 12/13/2023 File By: bob@partsync.com www.PartSync.com Flags: X=no-stuff T=Thru Hole H=Hand SMT E=Error

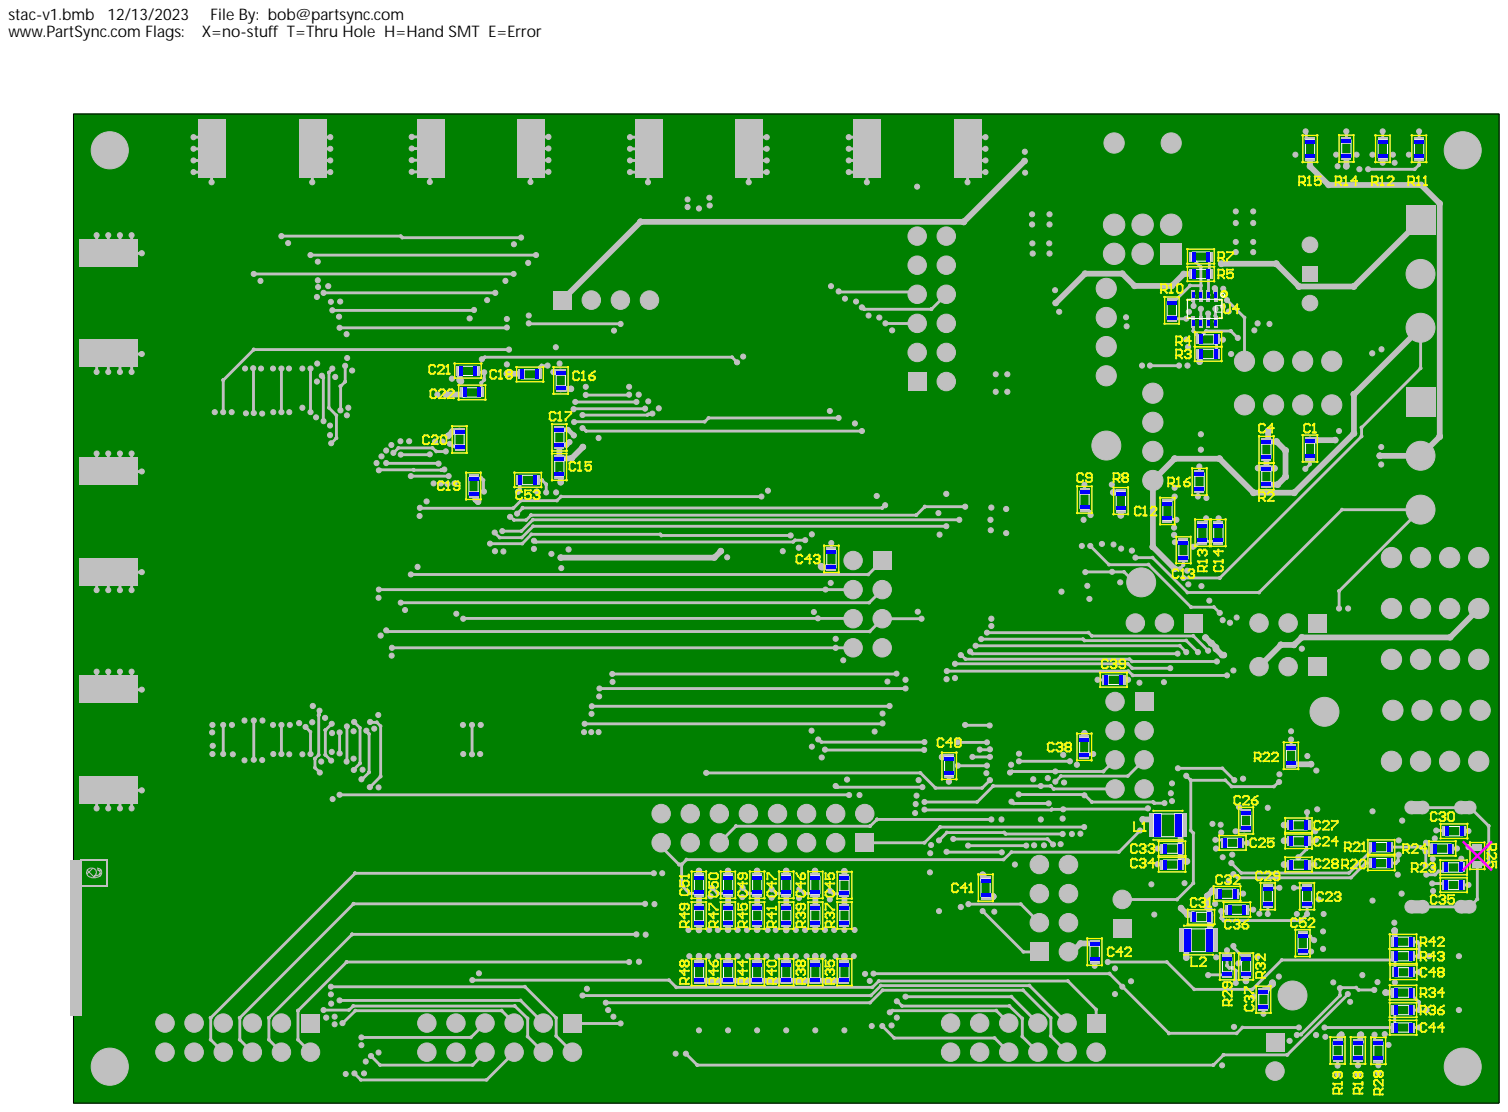
[picture p69: page 2]
