rahulk29/stac-pcb/v1-pcb/STAC_PCB/Schematics_pdf/231026_STAC-V1_schematics.PDF

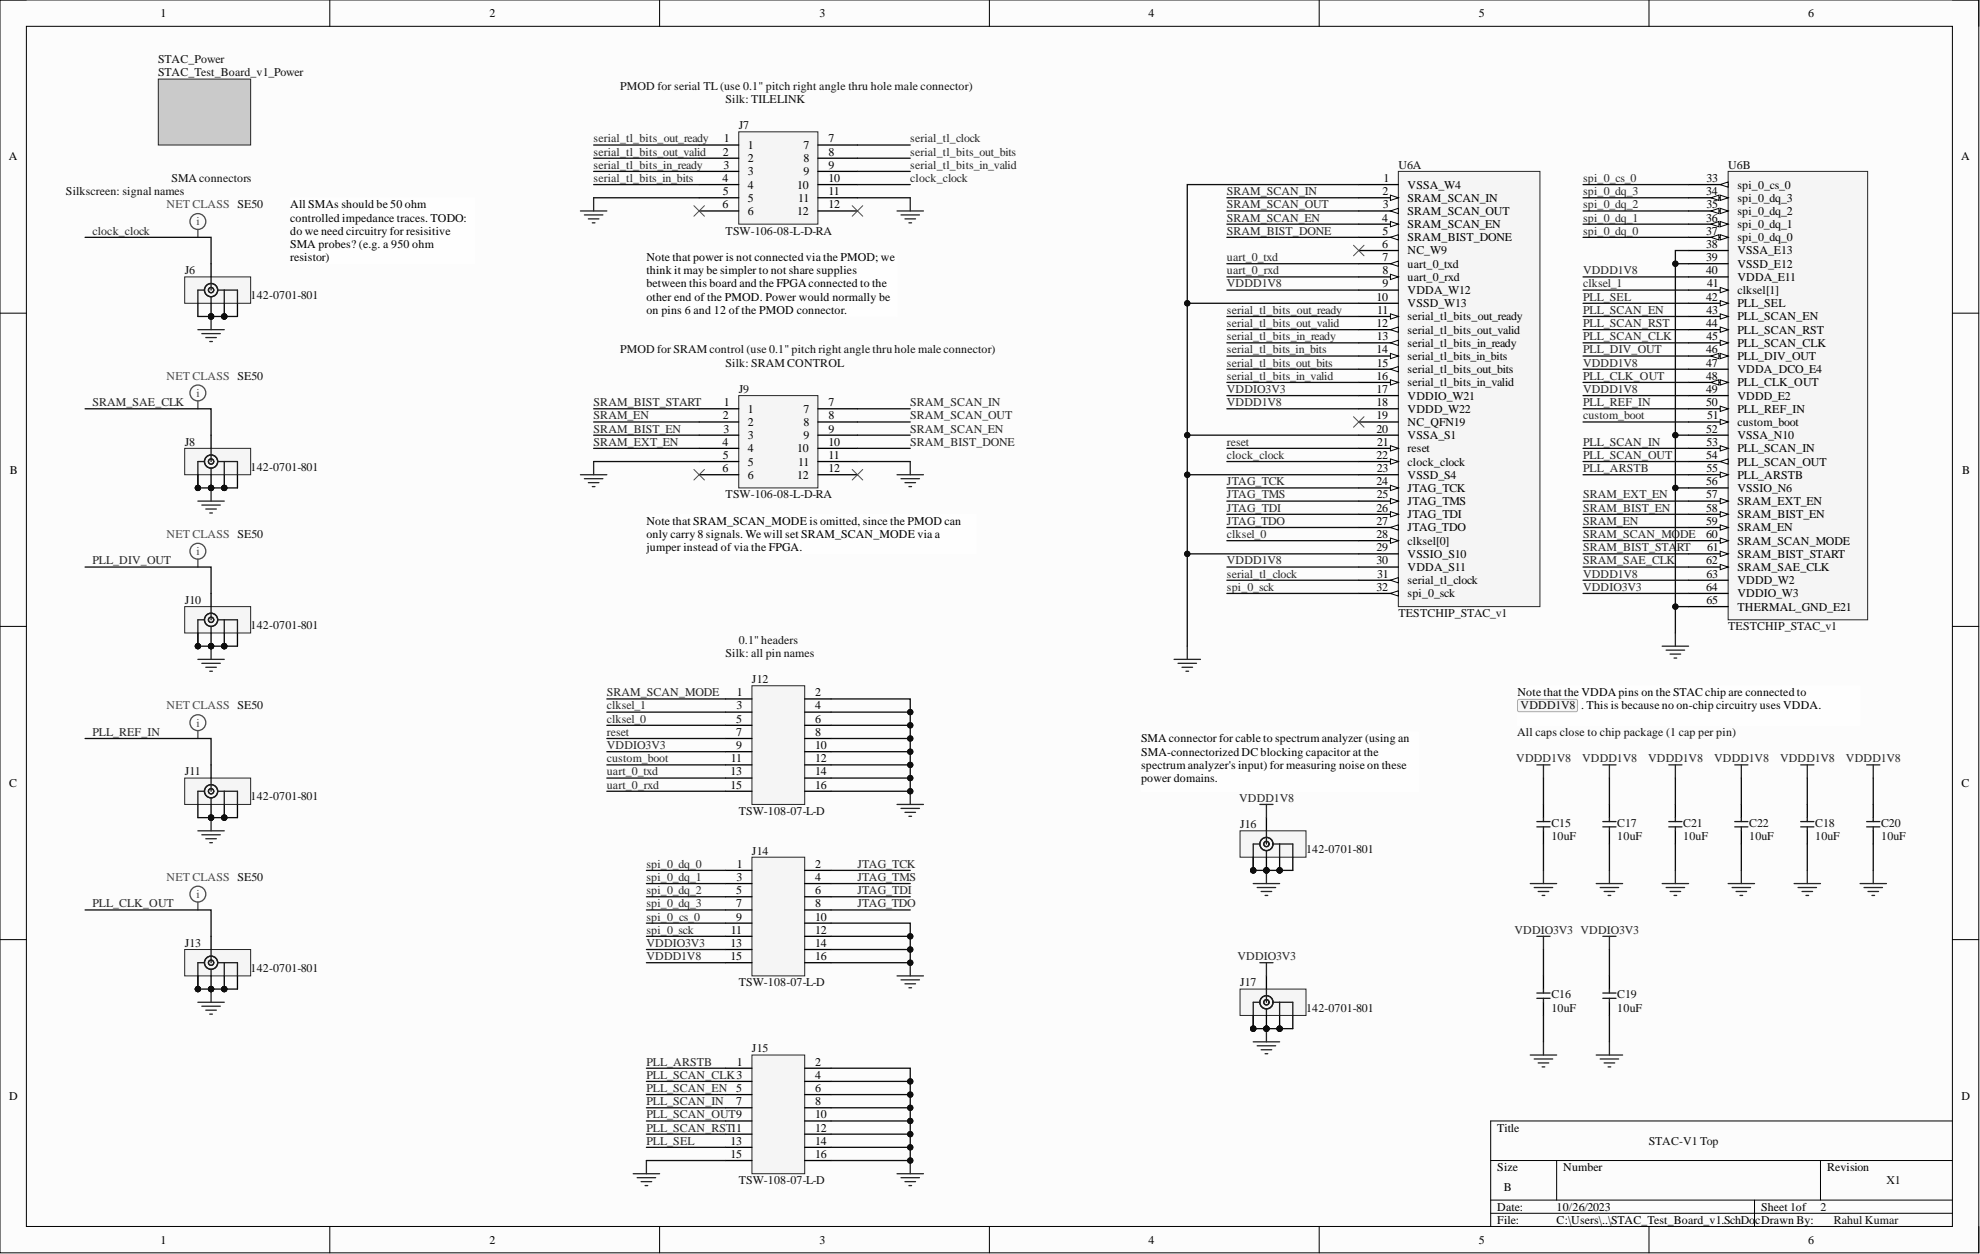
[picture p70: page 1]

1 0
1 2

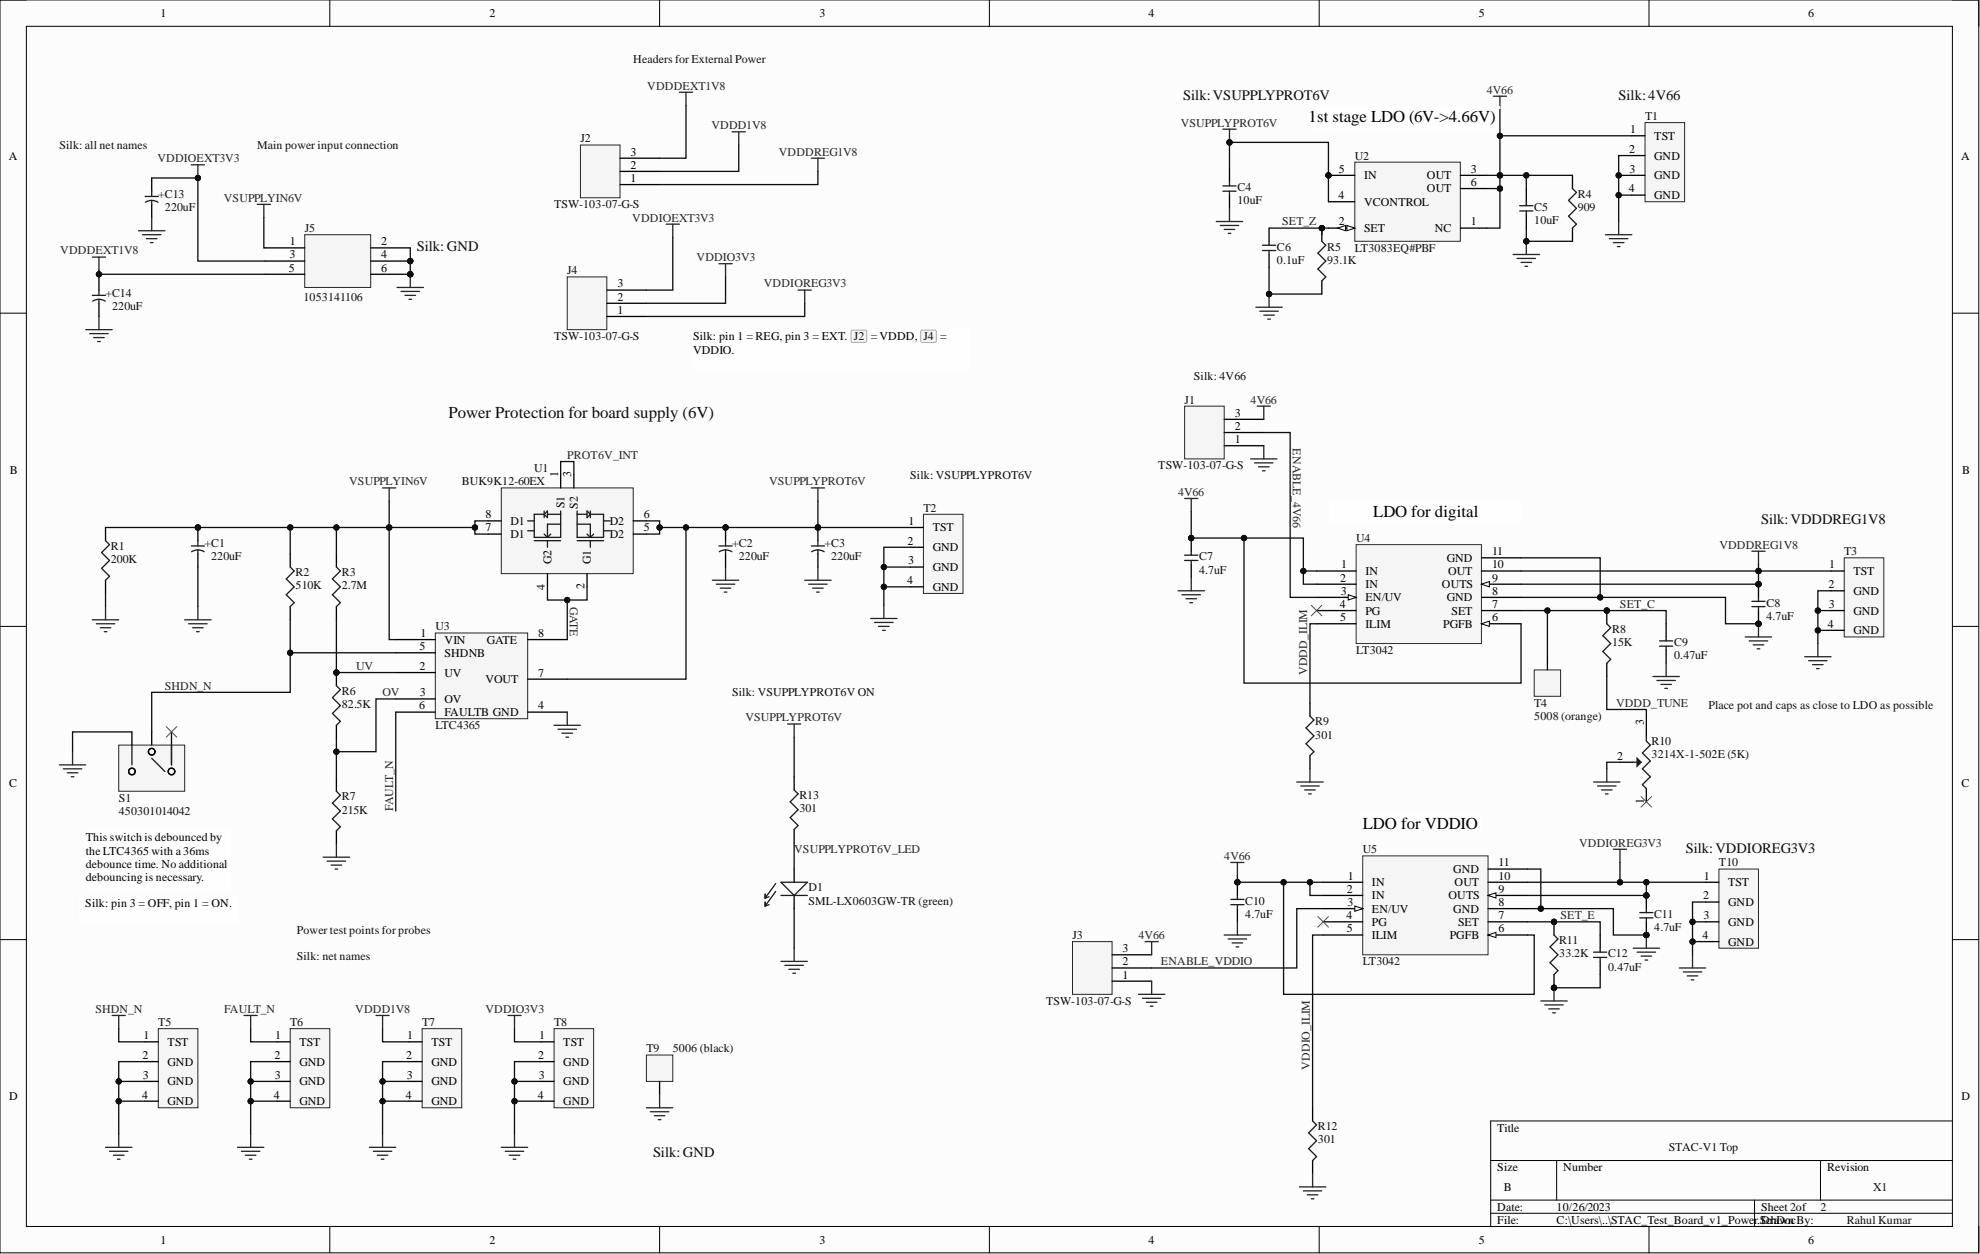
[picture p71: page 2]

ion for board supply (6V

E N ABL E _ V | 4 | SE T_E
