rahulk29/stac-pcb/schematic_review_v1/231027_schematics.pdf

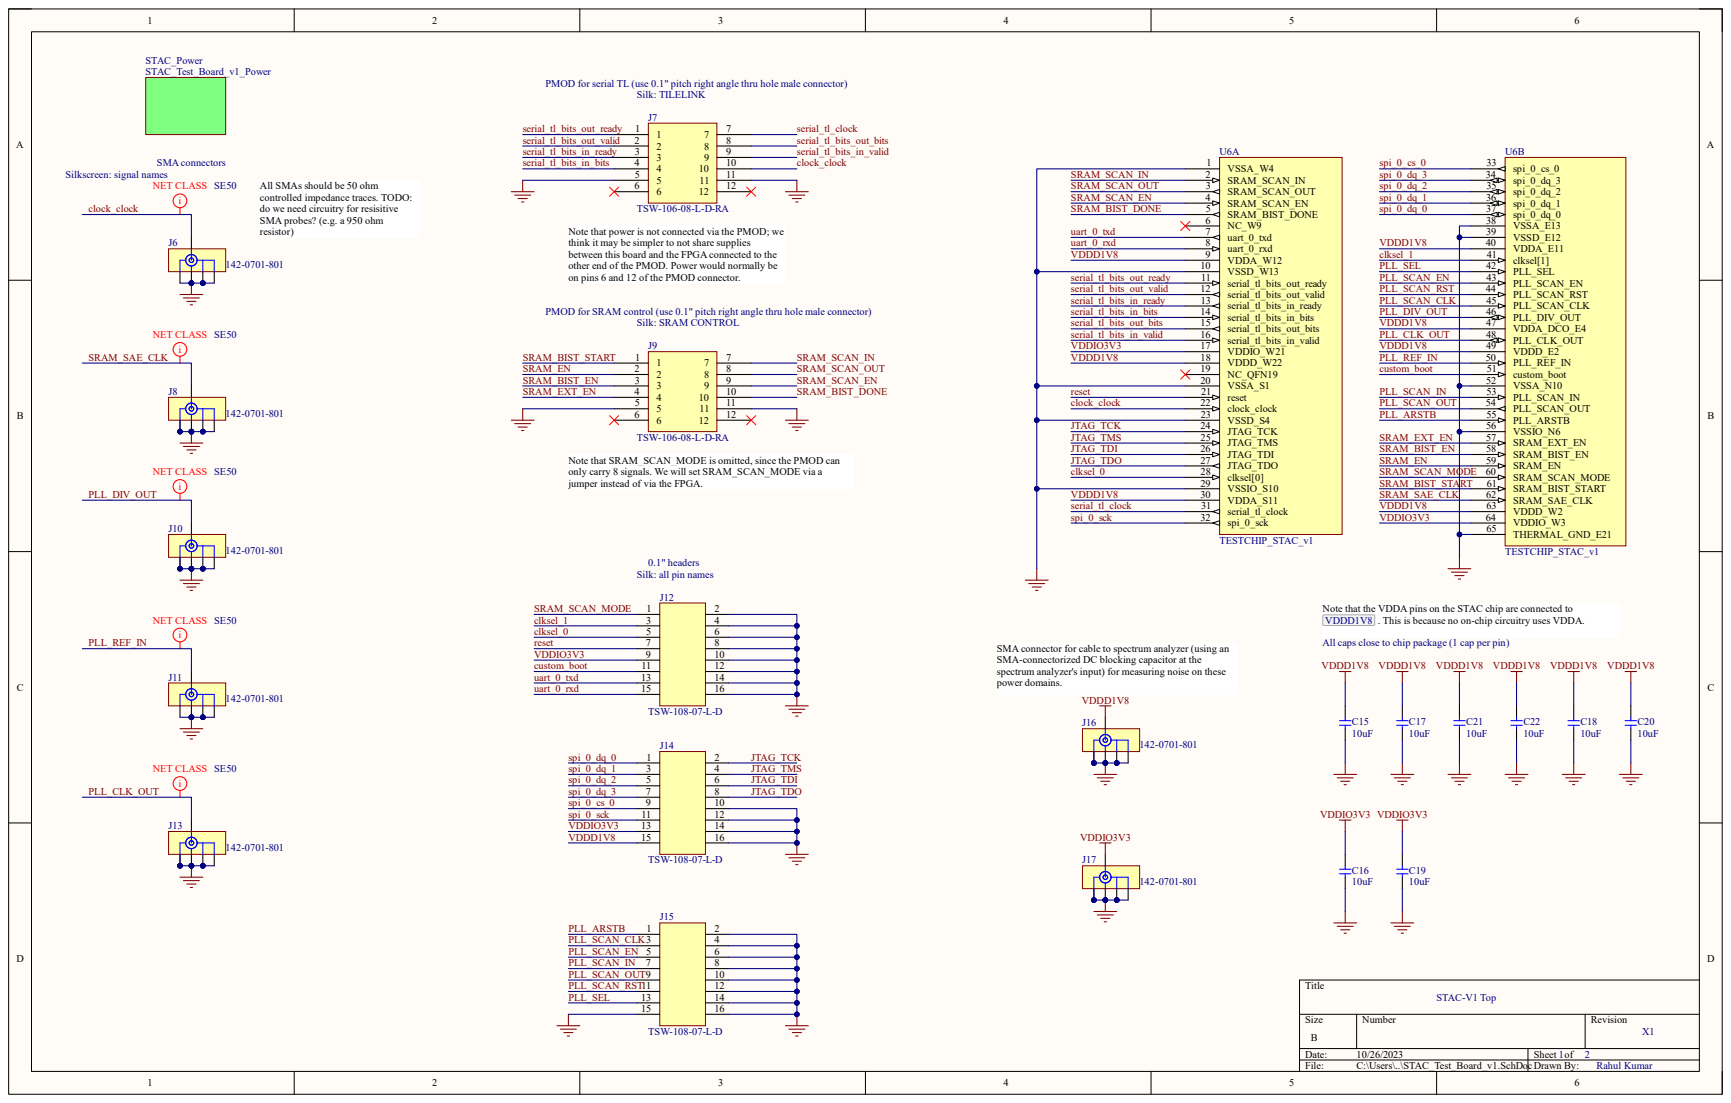
[picture p72: page 1]

PMOD for serial TL (use 0.1" pitch right angle thru hole male connector)

All SMAs should be 50 ohm
controlled impedance traces. TODO:
do we need circuitry for resisitive
SMA probes? (e.g. a 950 ohm
resistor)

Note that power is not connected via the PMOD; we
think it may be simpler to not share supplies
between this board and the FPGA connected to the
other end of the PMOD. Power would normally be
on pins 6 and 12 of the PMOD connector.

PMOD for SRAM control (use 0.1" pitch right angle thru hole male connector)

Note that SRAM_SCAN_MODE is omitted, since the PMOD can
only carry 8 signals. We will set SRAM_SCAN_MODE via a
jumper instead of via the FPGA.

0.1" headers
Silk: all pin names

Note that the VDDA pins on the STAC chip are connected to
VDDD1V8 . This is because no on-chip circuitry uses VDDA.

SMA connector for cable to spectrum analyzer (using an
SMA-connectorized DC blocking capacitor at the
spectrum analyzer's input) for measuring noise on these
power domains.

All caps close to chip package (1 cap per pin)

## 1st stage LDO (6V->4.66V)

Silk: VSUPPLYPROT6V | Silk: 4V66

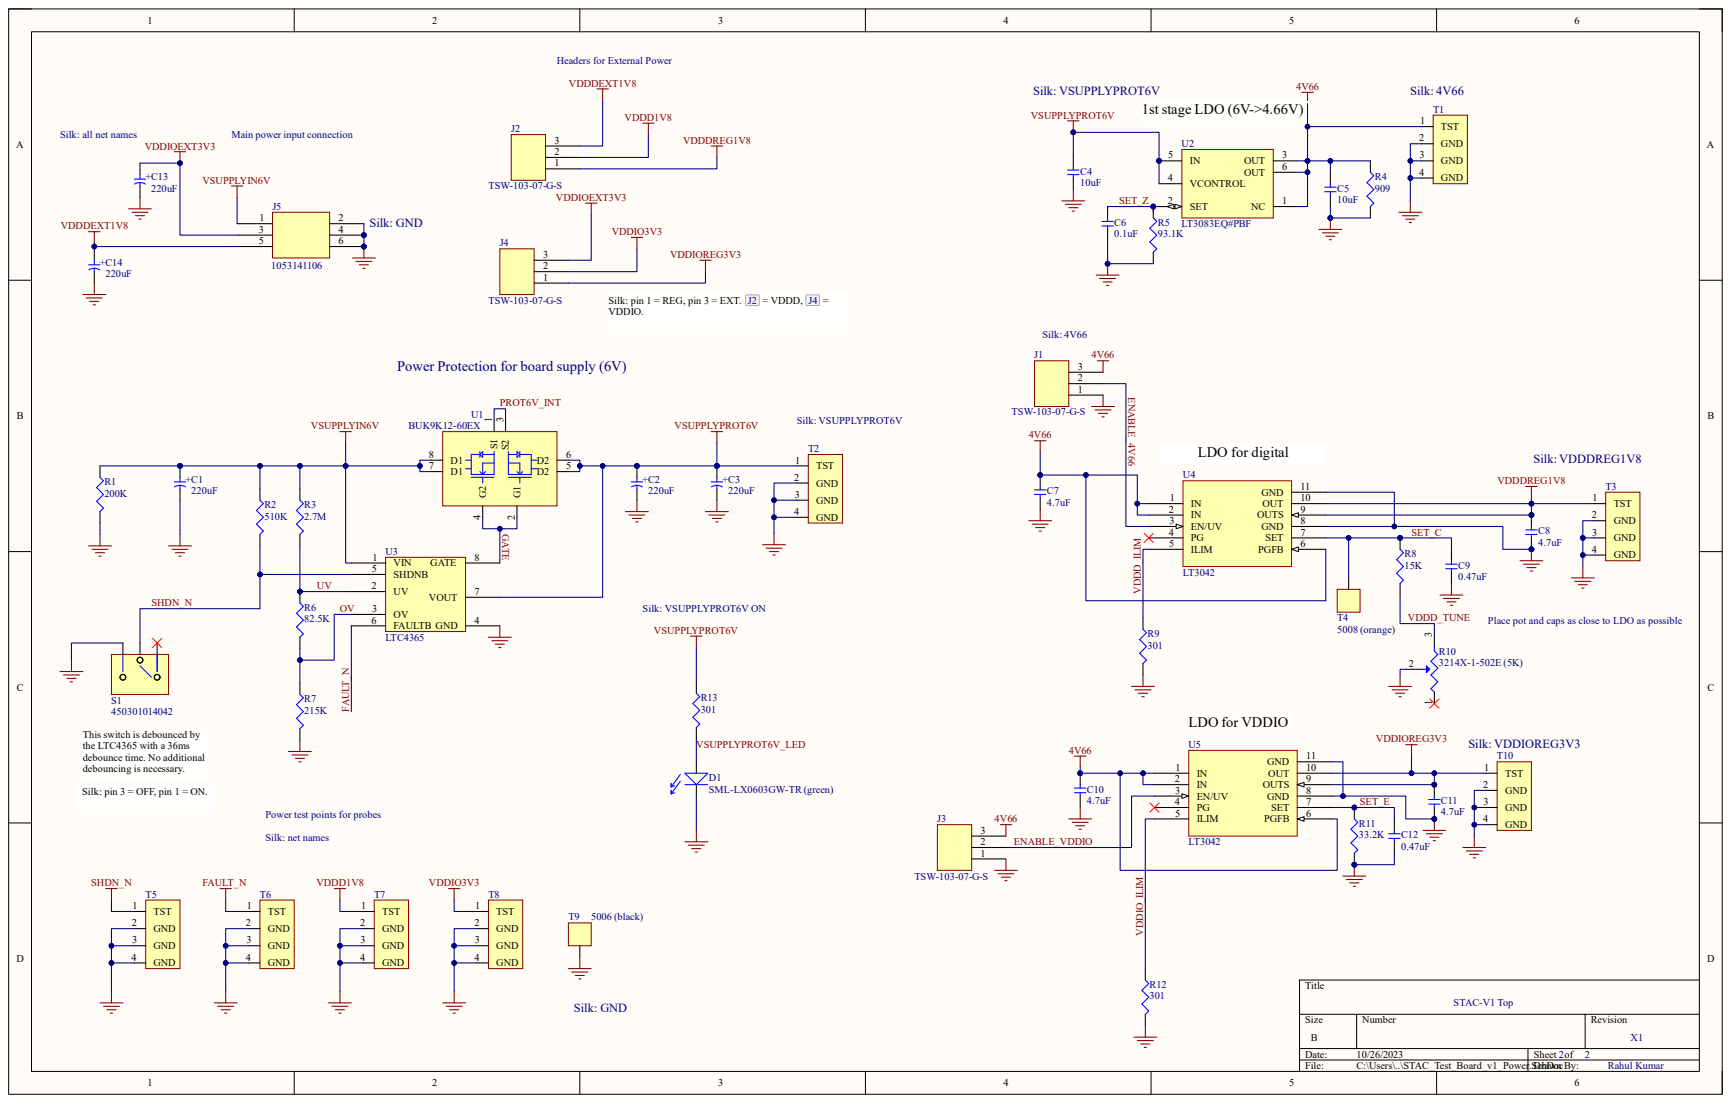
[picture p73: page 2]

Headers for External Power

Silk: all net names

Silk: pin 1 = REG, pin 3 = EXT. J2 = VDDD, J4 =
VDDIO.

Power Protection for board supply (6V)

Place pot and caps as close to LDO as possible

This switch is debounced by
the LTC4365 with a 36ms
debounce time. No additional
debouncing is necessary.

Silk: pin 3 = OFF, pin 1 = ON.

Power test points for probes
